blackjetrock/experimental-computer-for-schools/Documentation/1000038513.jpg

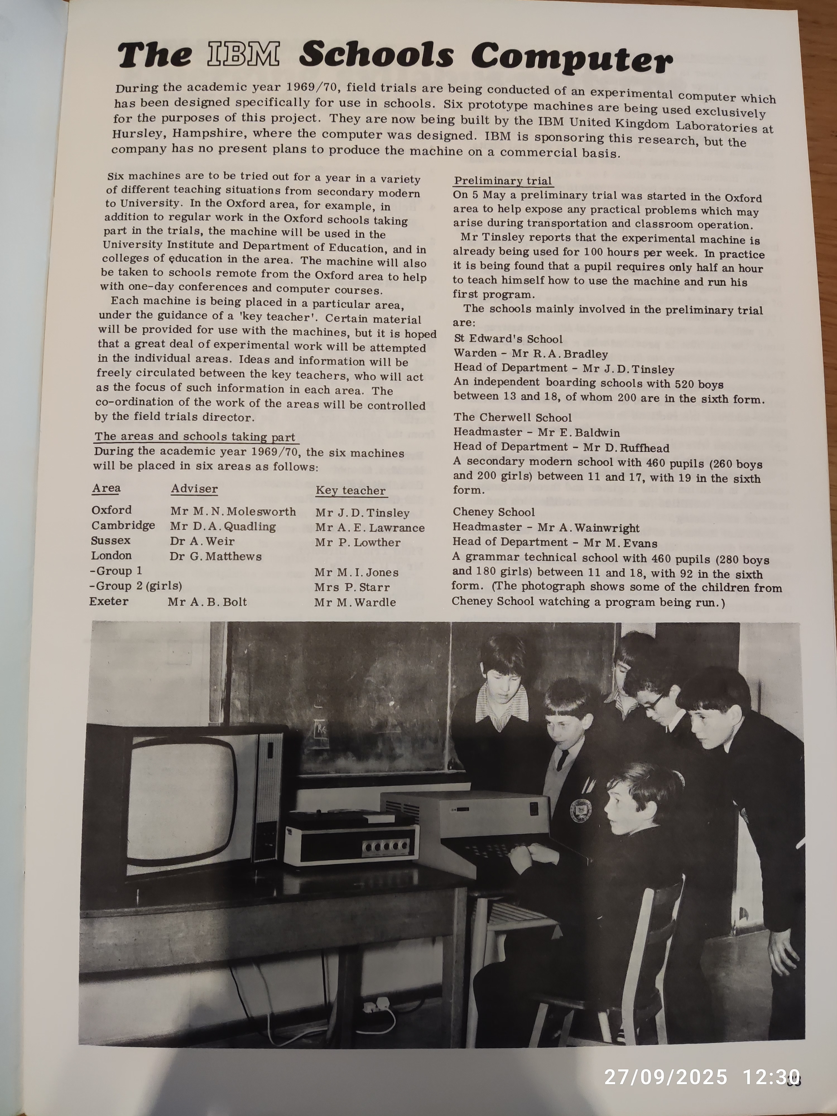
Documentation/1000038513.jpg
