blackjetrock/experimental-computer-for-schools/Documentation/1000038516.jpg

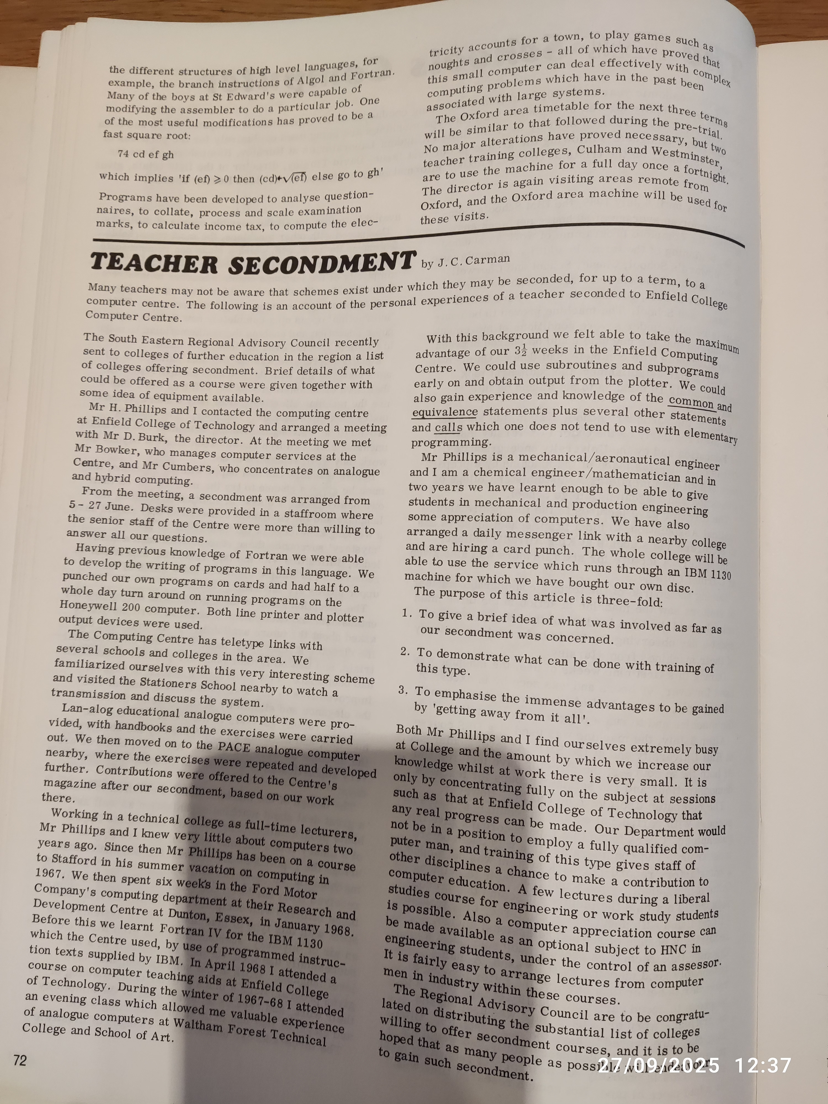
Documentation/1000038516.jpg
