blackjetrock/experimental-computer-for-schools/mechanical/front_panel_62mm_name_recess_only.dxf

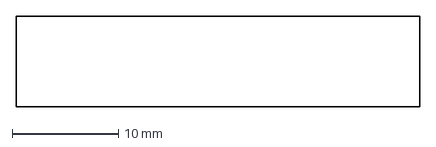
[picture p40: CAD file, 2024-07-29]
mechanical/front_panel_62mm_name_recess_only.dxf
38.0 x 8.50 mm
