blackjetrock/experimental-computer-for-schools/mechanical/3d_models/cased_desktop_left_support.stl

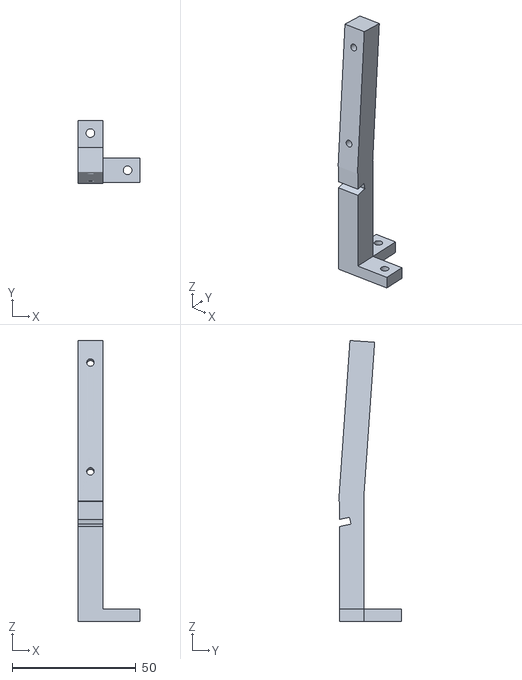
[picture p41: CAD file, 2024-07-29]
mechanical/3d_models/cased_desktop_left_support.stl
25.0 x 25.3 x 113.4
