blackjetrock/experimental-computer-for-schools/mechanical/switch_plate_cutout_1_0mm_tool.dxf

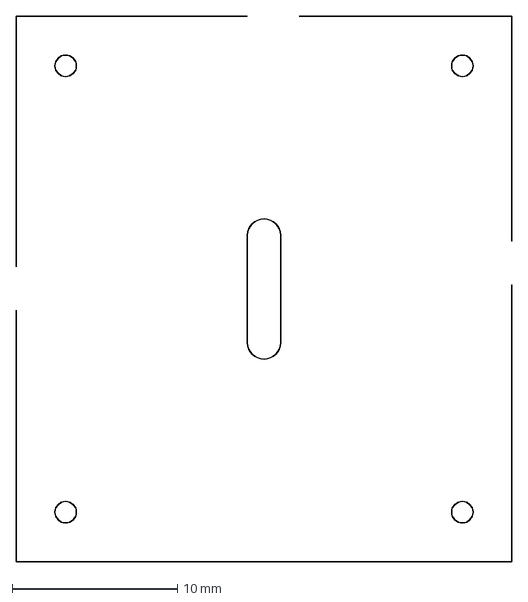
[picture p42: CAD file, 2024-07-29]
mechanical/switch_plate_cutout_1_0mm_tool.dxf
30.0 x 33.0 mm
