blackjetrock/experimental-computer-for-schools/mechanical/3d_models/television_rear_bottom_panel_v2.stl

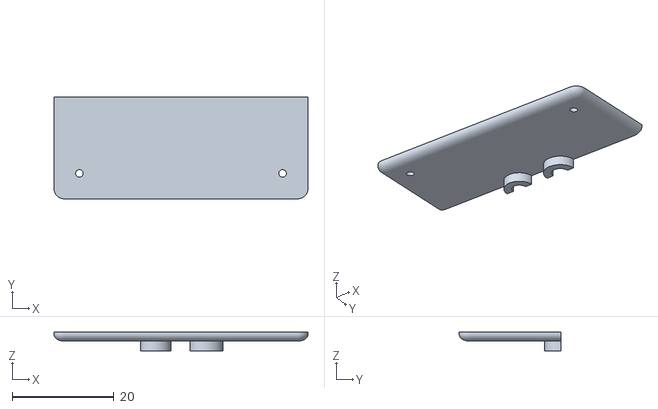
[picture p43: CAD file, 2024-07-29]
mechanical/3d_models/television_rear_bottom_panel_v2.stl
50.0 x 20.0 x 3.65
