blackjetrock/experimental-computer-for-schools/mechanical/switch_plate_cutout_1_5mm_tool.dxf

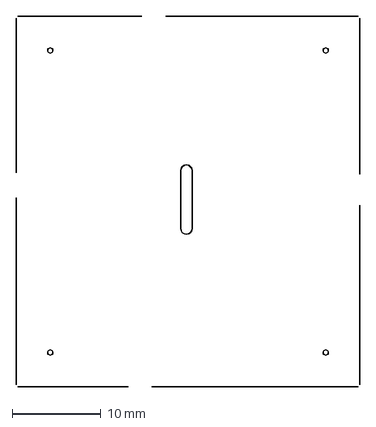
[picture p44: CAD file, 2024-07-23]
mechanical/switch_plate_cutout_1_5mm_tool.dxf
38.7 x 41.7 mm
