blackjetrock/experimental-computer-for-schools/mechanical/3d_models/desktop_pcb_standoff.stl

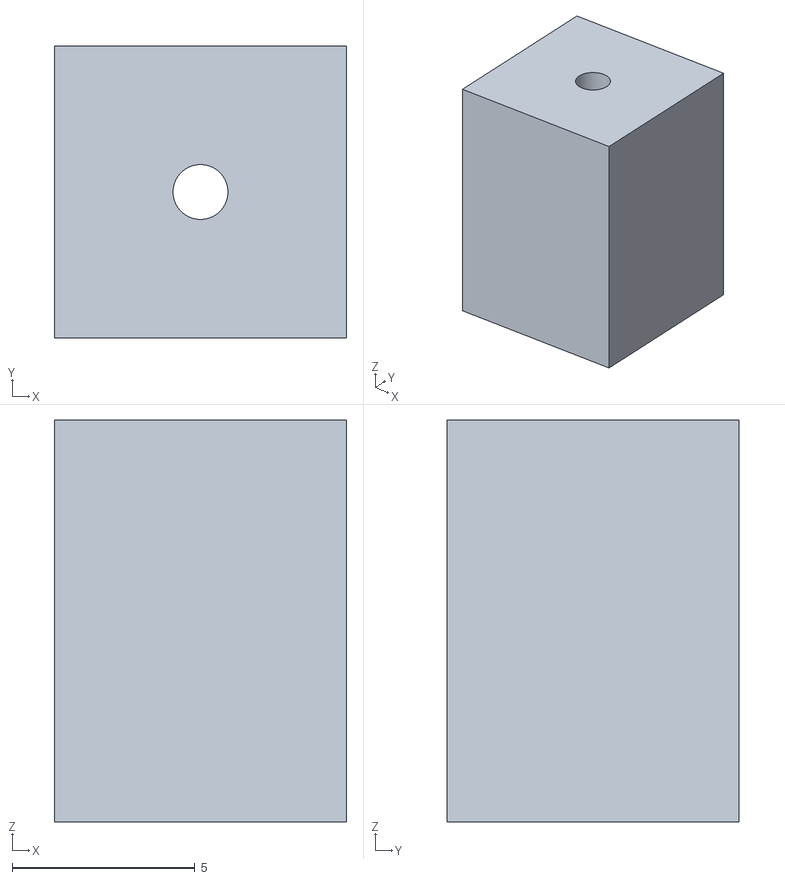
[picture p45: CAD file, 2024-07-29]
mechanical/3d_models/desktop_pcb_standoff.stl
8.00 x 8.00 x 11.0
