blackjetrock/experimental-computer-for-schools/mechanical/switch_plate_cutout.dxf

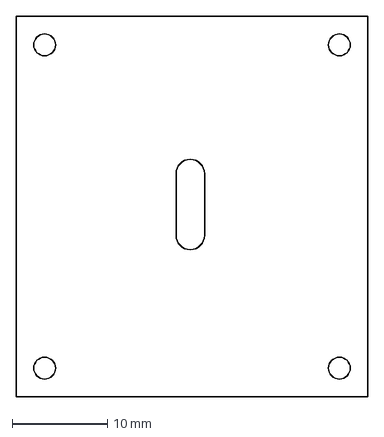
[picture p46: CAD file, 2024-07-23]
mechanical/switch_plate_cutout.dxf
37.0 x 40.0 mm
