blackjetrock/experimental-computer-for-schools/mechanical/3d_models/television_bezel_v2.stl

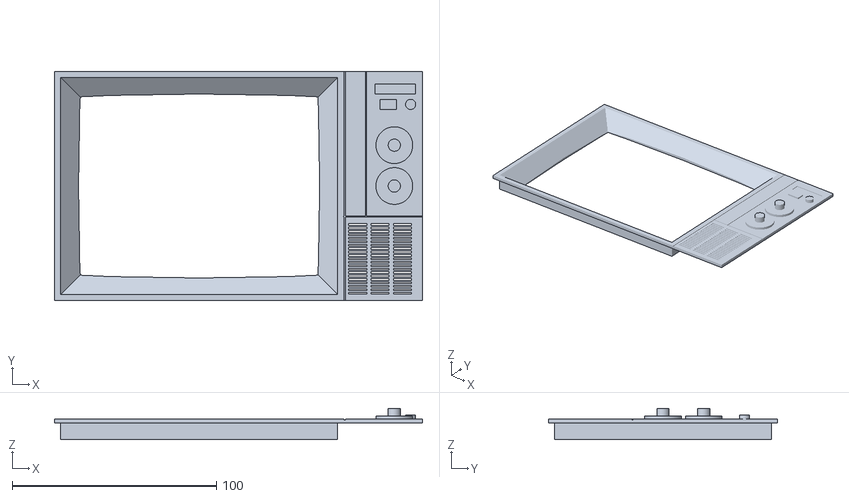
[picture p47: CAD file, 2024-07-29]
mechanical/3d_models/television_bezel_v2.stl
180.3 x 112.4 x 15.3
