blackjetrock/experimental-computer-for-schools/mechanical/front_panel_0mm_tool.dxf

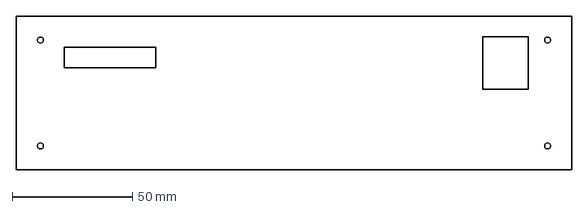
[picture p48: CAD file, 2024-07-23]
mechanical/front_panel_0mm_tool.dxf
231.0 x 64.0 mm
