blackjetrock/experimental-computer-for-schools/mechanical/3d_models/tv_spacer_corner.stl

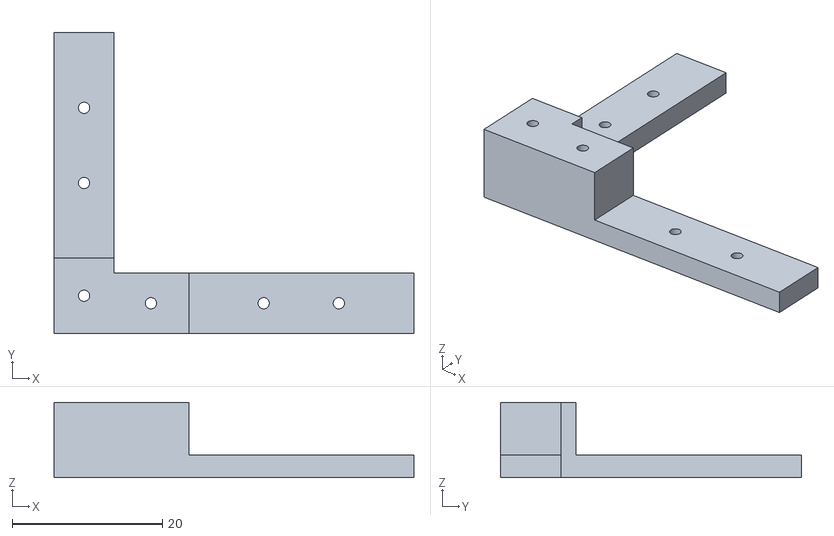
[picture p49: CAD file, 2024-07-29]
mechanical/3d_models/tv_spacer_corner.stl
47.9 x 40.0 x 10.0
