blackjetrock/experimental-computer-for-schools/mechanical/name_plate_vinyl_base_file.dxf

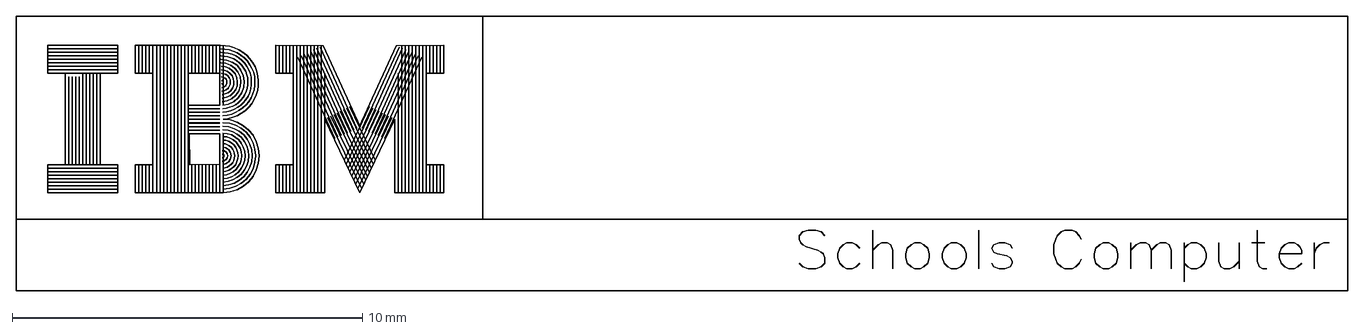
[picture p50: CAD file, 2024-07-23]
mechanical/name_plate_vinyl_base_file.dxf
38.0 x 7.83 mm
