blackjetrock/experimental-computer-for-schools/mechanical/name_plate_writing_borders.dxf

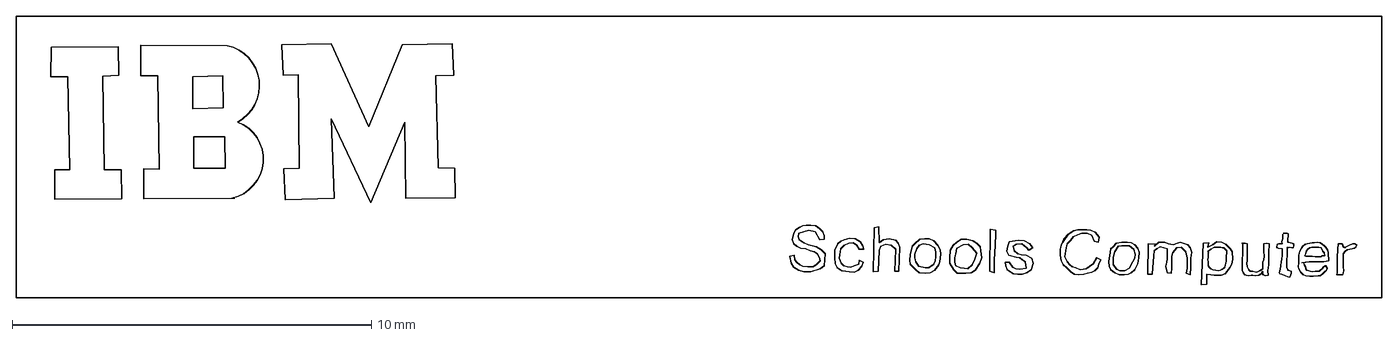
[picture p51: CAD file, 2024-07-23]
mechanical/name_plate_writing_borders.dxf
38.0 x 7.83 mm
