blackjetrock/experimental-computer-for-schools/mechanical/3d_models/overlay_and_front_panel_alignment.dxf

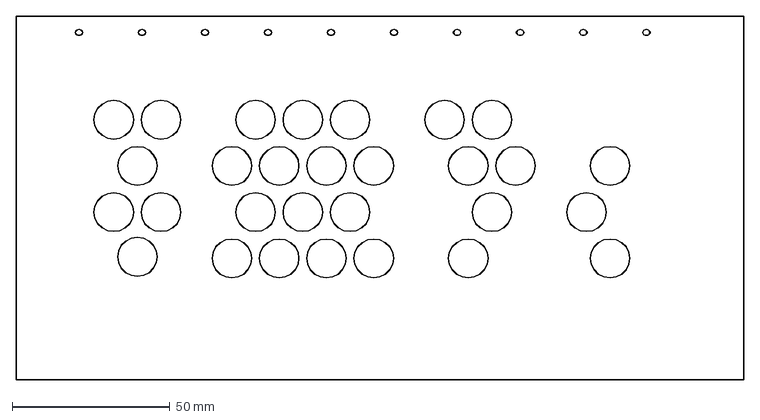
[picture p52: CAD file, 2024-07-01]
mechanical/3d_models/overlay_and_front_panel_alignment.dxf
231.0 x 115.4 mm
