blackjetrock/experimental-computer-for-schools/mechanical/name_plate_writing_borders_lines_tidy_filled_text_only.dxf

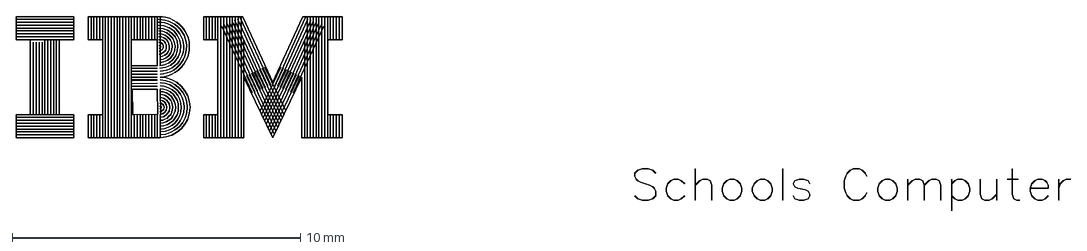
[picture p53: CAD file, 2024-07-23]
mechanical/name_plate_writing_borders_lines_tidy_filled_text_only.dxf
36.6 x 6.75 mm
