blackjetrock/experimental-computer-for-schools/mechanical/3d_models/cased_desktop.dxf

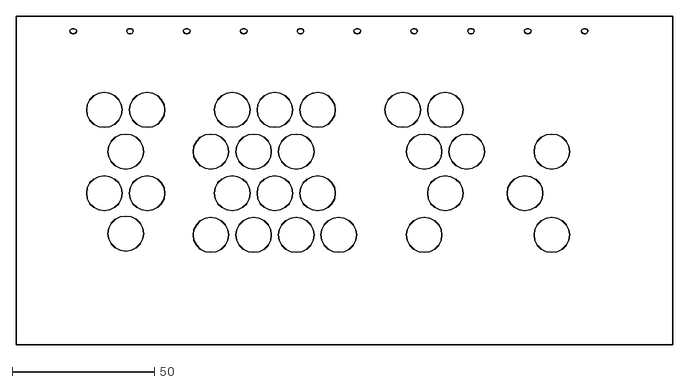
[picture p54: CAD file, 2024-07-01]
mechanical/3d_models/cased_desktop.dxf
231.0 x 115.4
