blackjetrock/experimental-computer-for-schools/mechanical/name_plate_writing_borders_lines_tidy_filled.dxf

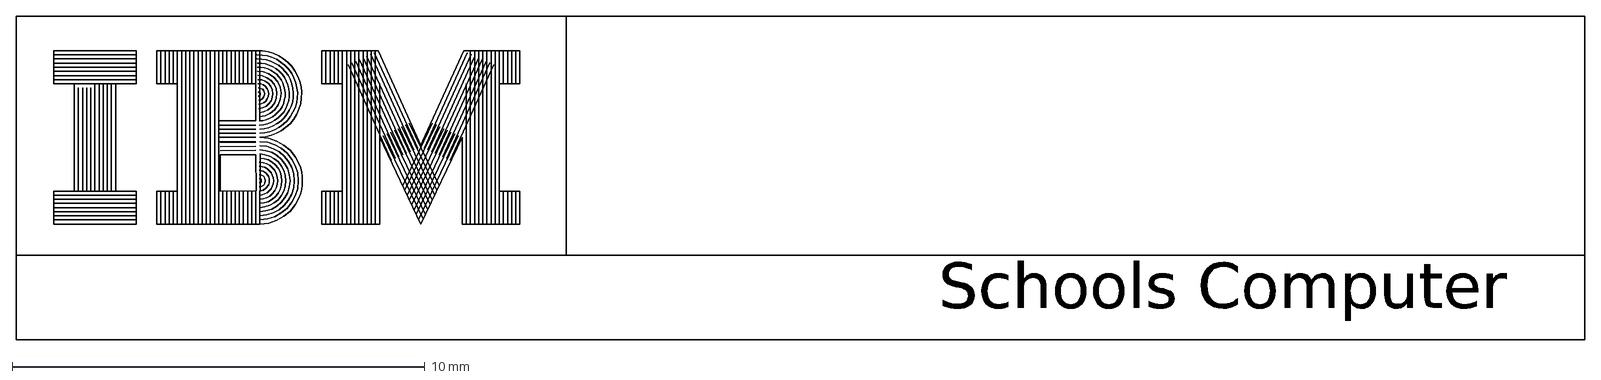
[picture p55: CAD file, 2024-07-23]
mechanical/name_plate_writing_borders_lines_tidy_filled.dxf
Schools Computer
