blackjetrock/experimental-computer-for-schools/mechanical/name_plate_writing_borders_lines_tidy.dxf

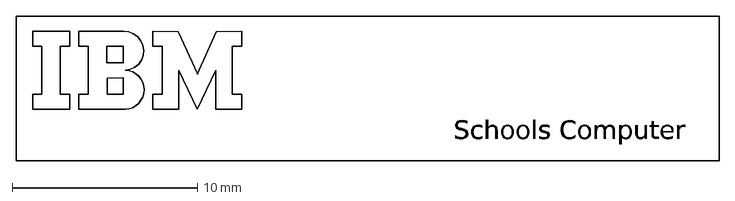
[picture p56: CAD file, 2024-07-23]
mechanical/name_plate_writing_borders_lines_tidy.dxf
Schools Computer
