blackjetrock/experimental-computer-for-schools/mechanical/switch_plate_cutout_1_3mm_tool.dxf

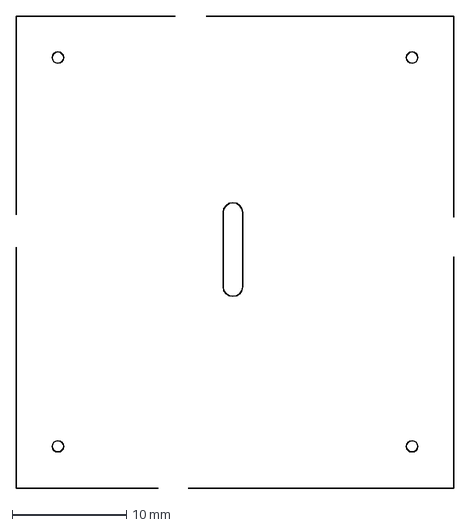
[picture p57: CAD file, 2024-07-23]
mechanical/switch_plate_cutout_1_3mm_tool.dxf
38.3 x 41.3 mm
