blackjetrock/experimental-computer-for-schools/mechanical/front_panel_3mm_tool.dxf

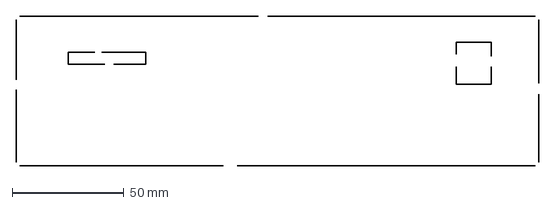
[picture p58: CAD file, 2024-07-23]
mechanical/front_panel_3mm_tool.dxf
234.2 x 67.2 mm
