blackjetrock/experimental-computer-for-schools/mechanical/name_plate.dxf

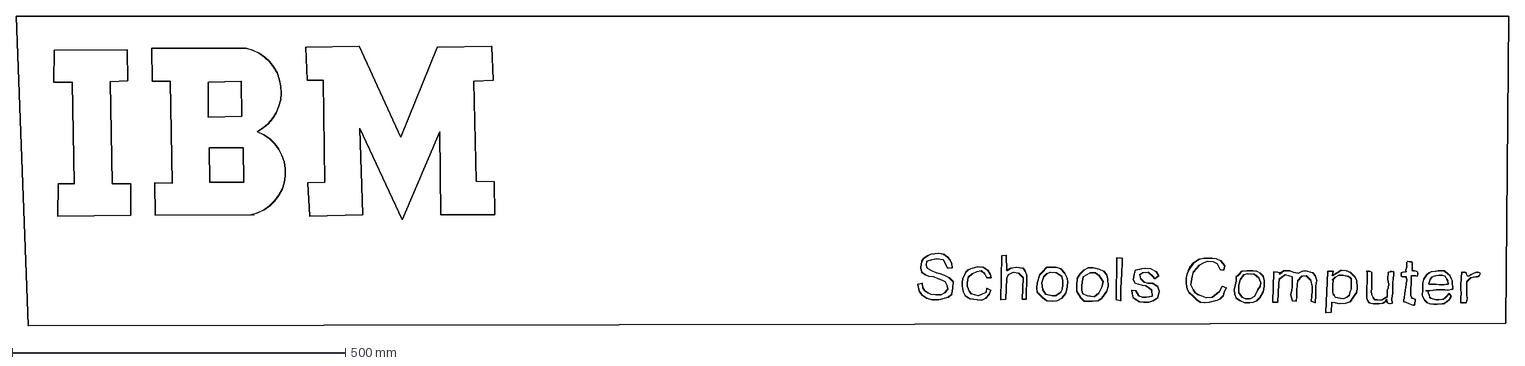
[picture p59: CAD file, 2024-07-23]
mechanical/name_plate.dxf
2239.5 x 463.9 mm
