blackjetrock/experimental-computer-for-schools/mechanical/name_plate_writing_borders_lines_tidy_filled_colour_limits_only.dxf

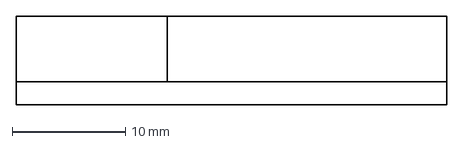
[picture p60: CAD file, 2024-07-23]
mechanical/name_plate_writing_borders_lines_tidy_filled_colour_limits_only.dxf
38.0 x 7.83 mm
