blackjetrock/experimental-computer-for-schools/mechanical/name_plate_writing.dxf

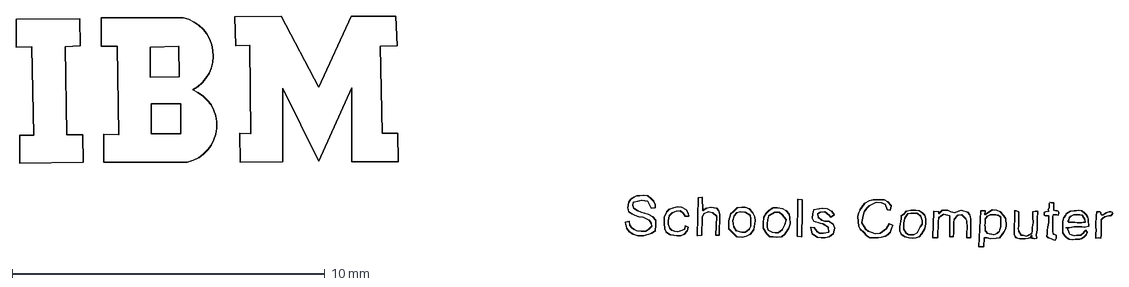
[picture p61: CAD file, 2024-07-23]
mechanical/name_plate_writing.dxf
35.0 x 7.37 mm
