blackjetrock/experimental-computer-for-schools/mechanical/switch_plate_cutout_1mm_tool.dxf

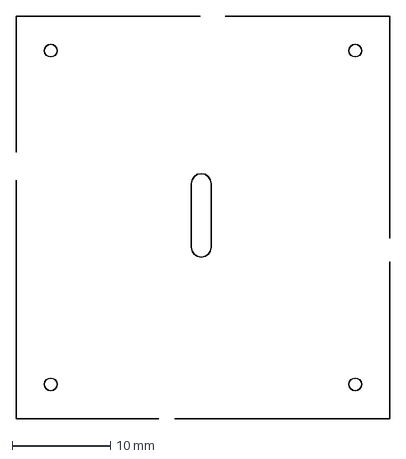
[picture p62: CAD file, 2024-07-23]
mechanical/switch_plate_cutout_1mm_tool.dxf
38.0 x 41.0 mm
