blackjetrock/experimental-computer-for-schools/mechanical/switch_plate_text.dxf

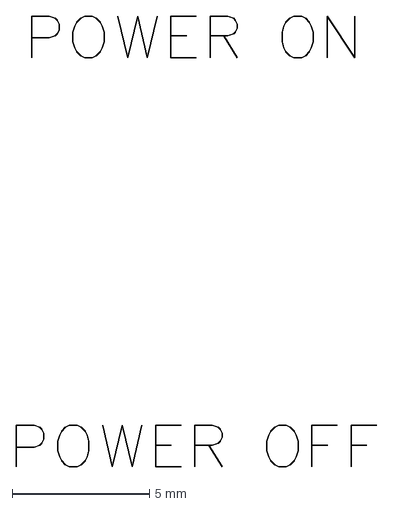
[picture p63: CAD file, 2024-07-23]
mechanical/switch_plate_text.dxf
13.1 x 16.4 mm
