blackjetrock/experimental-computer-for-schools/mechanical/switch_plate.dxf

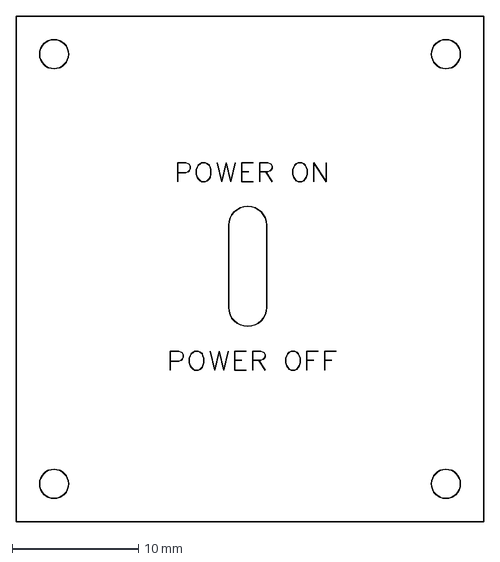
[picture p64: CAD file, 2024-07-23]
mechanical/switch_plate.dxf
37.0 x 40.0 mm
