blackjetrock/experimental-computer-for-schools/mechanical/Untitled.dxf

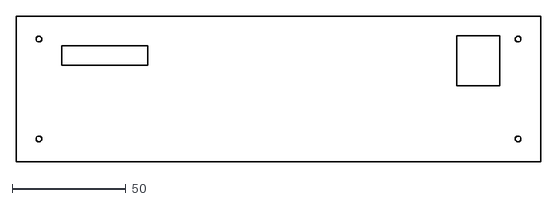
[picture p65: CAD file, 2024-07-16]
mechanical/Untitled.dxf
231.0 x 64.0
