blackjetrock/experimental-computer-for-schools/mechanical/front_panel2.dxf

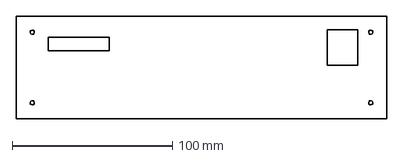
[picture p66: CAD file, 2024-07-16]
mechanical/front_panel2.dxf
231.0 x 64.0 mm
