blackjetrock/experimental-computer-for-schools/mechanical/test.dxf

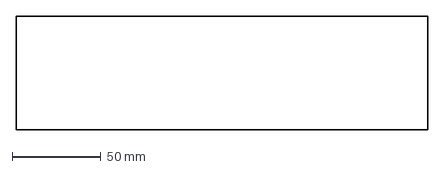
[picture p67: CAD file, 2024-07-16]
mechanical/test.dxf
231.0 x 64.0 mm
