blackjetrock/experimental-computer-for-schools/mechanical/front_panel_cnc_tool_1_3mm.dxf

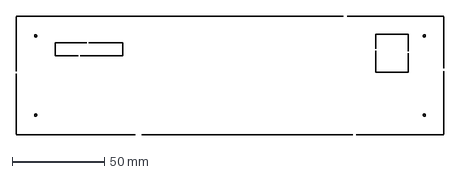
[picture p68: CAD file, 2024-07-16]
mechanical/front_panel_cnc_tool_1_3mm.dxf
232.3 x 64.3 mm
