blackjetrock/experimental-computer-for-schools/mechanical/front_panel.dxf

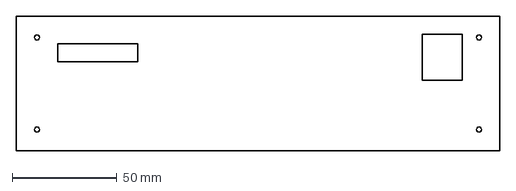
[picture p69: CAD file, 2024-07-16]
mechanical/front_panel.dxf
231.0 x 64.0 mm
