blackjetrock/experimental-computer-for-schools/mechanical/front_panel_cnc_tool_1_0mm.dxf

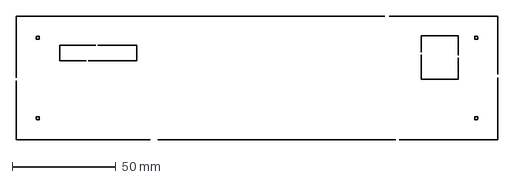
[picture p70: CAD file, 2024-07-14]
mechanical/front_panel_cnc_tool_1_0mm.dxf
232.0 x 59.6 mm
