blackjetrock/experimental-computer-for-schools/mechanical/esc_desktop_case_grill_cnc.dxf

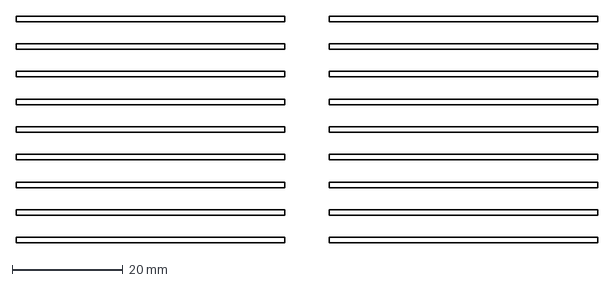
[picture p71: CAD file, 2024-07-14]
mechanical/esc_desktop_case_grill_cnc.dxf
105.0 x 41.0 mm
