blackjetrock/experimental-computer-for-schools/mechanical/name_panel.dxf

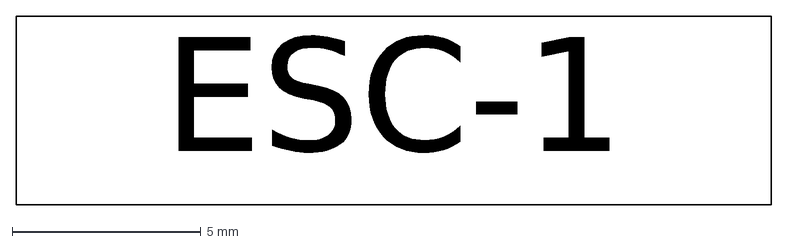
[picture p73: CAD file, 2024-07-13]
mechanical/name_panel.dxf
ESC-1
