blackjetrock/experimental-computer-for-schools/mechanical/knob_label_1.dxf

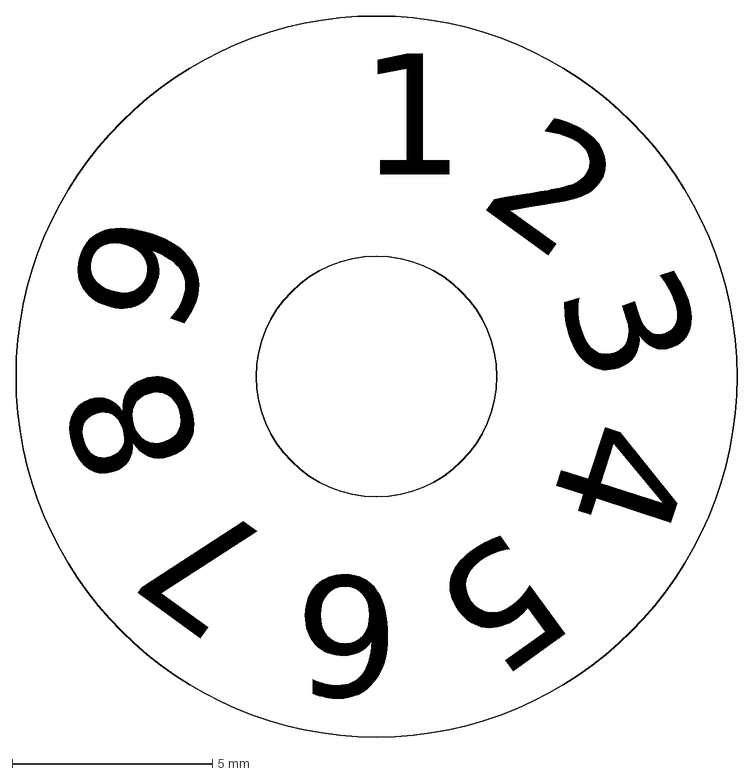
[picture p74: CAD file, 2024-07-13]
mechanical/knob_label_1.dxf
1
3
2
4
5
6
7
8
9
