blackjetrock/experimental-computer-for-schools/mechanical/knob_label_2.dxf

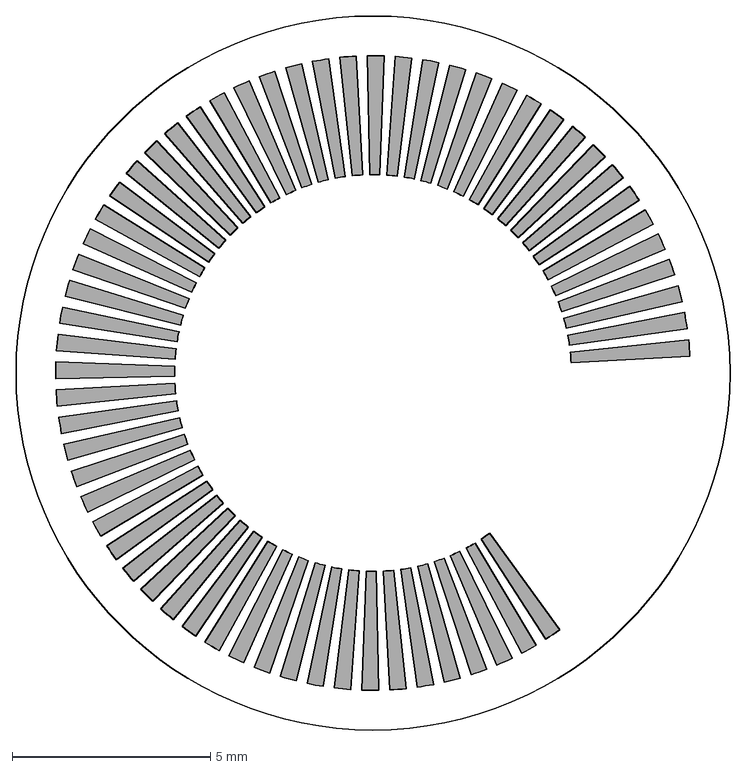
[picture p75: CAD file, 2024-07-13]
mechanical/knob_label_2.dxf
18.0 x 18.0 mm
