blackjetrock/experimental-computer-for-schools/mechanical/kb_holes.dxf

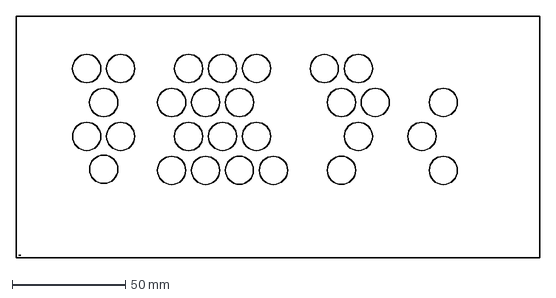
[picture p76: CAD file, 2024-06-30]
mechanical/kb_holes.dxf
231.0 x 106.5 mm
