blackjetrock/experimental-computer-for-schools/mechanical/kb_holes_bevelled.dxf

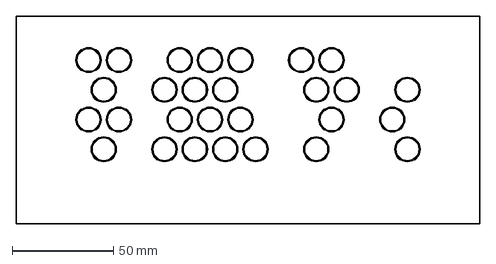
[picture p77: CAD file, 2024-06-29]
mechanical/kb_holes_bevelled.dxf
229.0 x 102.3 mm
