blackjetrock/experimental-computer-for-schools/firmware/pico_main/experimental_schools_computer.c

//////////////////////////////////////////////////////////////////////////////
//
// Experimental Schools Computer Simulator
//
////////////////////////////////////////////////////////////////////////////////
//
// Simulates the IBM experimental schools computer
//
// Runs on RP Pico
// 0.96" OLED display
// Tactile switch keys
//
// USB CLI
// Wifi hot spot with screen display 
//
////////////////////////////////////////////////////////////////////////////////

#include "switches.h"
#include "version.h"

#pragma GCC diagnostic ignored "-Wwrite-strings"

#include <ctype.h>
#include <math.h>
#include <stdarg.h>
#include <stdio.h>
#include <stdlib.h>
#include <string.h>
#include <stdint.h>

#include "pico/stdlib.h"
#include "hardware/pio.h"
#include "hardware/dma.h"
#include "hardware/irq.h"
#include "hardware/flash.h"
#include "hardware/clocks.h"
#include "hardware/structs/bus_ctrl.h"

#define DEBUG_STOP_LOOP while(1) {}

// Some logic to analyse:

#include "hardware/structs/pwm.h"
#include "pico/multicore.h"
#include "pico/bootrom.h"

#include "oled.h"
#include "sdcard.h"

#include "fsms.h"
#include "esc_fsms.h"

#include "esc.h"
#include "esc_desktop_display.h"
#include "extracode.h"

////////////////////////////////////////////////////////////////////////////////

int status[7];
int kbd_scan_code = 0;

#define CHAR_MS_DELAY 20

//------------------------------------------------------------------------------
//
// Decode key tokens
//

KEY_INFO key_info[] =
  {
    {"KI RESET   ", TOK_KEY_KI_RESET},
    {"A          ", TOK_KEY_A},
    {"B          ", TOK_KEY_B},
    {"C          ", TOK_KEY_C},
    {"0          ", TOK_KEY_0},
    {"1          ", TOK_KEY_1},
    {"2          ", TOK_KEY_2},
    {"3          ", TOK_KEY_3},
    {"4          ", TOK_KEY_4},
    {"5          ", TOK_KEY_5},
    {"6          ", TOK_KEY_6},
    {"7          ", TOK_KEY_7},
    {"8          ", TOK_KEY_8},
    {"9          ", TOK_KEY_9},
    {"RUN        ", TOK_KEY_RUN},
    {"STOP       ", TOK_KEY_STOP},
    {"RELOAD     ", TOK_KEY_RELOAD},
    {"CHECK      ", TOK_KEY_CHECK},
    {"DUMP       ", TOK_KEY_DUMP},
    {"LOAD IAR   ", TOK_KEY_LOAD_IAR},
    {"LOAD ADDR  ", TOK_KEY_LOAD_ADDR},
    {"LOAD STORE ", TOK_KEY_LOAD_STORE},
    {"DECR ADDR  ", TOK_KEY_DECR_ADDR},
    {"INCR ADDR  ", TOK_KEY_INCR_ADDR},
    {"NORM RESET ", TOK_KEY_NORMAL_RESET},
    {"CLEAR      ", TOK_KEY_CLEAR},
    {"DOT        ", TOK_KEY_DOT},
    {"MINUS      ", TOK_KEY_MINUS},
  };

#define NUM_KEY_INFO (sizeof(key_info)/sizeof(KEY_INFO))

char *key_name(int tok)
{
  for(int i=0; i<NUM_KEY_INFO; i++)
    {
      if( key_info[i].tok == tok )
        {
          return(key_info[i].name);
        }
    }
  return("????");
}

////////////////////////////////////////////////////////////////////////////////
//
// Tests
//

#define MAX_TEST_FAIL_BUFFER 160

// Initialise registers and store
typedef enum _INIT_CODE
  {
    IC_SET_REG_N = 10,
    IC_SET_REG_V,
    IC_SET_STORE_A,
    IC_SET_STORE_V,
    IC_END,
  } INIT_CODE;

typedef struct _INIT_INFO
{
  INIT_CODE code;
  uint64_t   n;
} INIT_INFO;

// The following enum is also used to identify registers other than R0..9
// when testing results. E.g. IAR

typedef enum _TEST_CODE
  {
    TC_REG_N = 20,
    TC_REG_IAR,
    TC_REG_LINK,
    TC_REG_ADDR,
    TC_CL,
    TC_REG_KI,
    TC_STORE_N,
    TC_MUST_BE,
    TC_MUST_BE_STOPPED,
    TC_MUST_BE_NOT_STOPPED,
    TC_END_SECTION,    // End of sub section results. Check up to here (or a TC_END) by TOK_TEST_CHECK_RES token
    // Do not put a spurious TC_SECTION_END before a TC_END
    TC_END,
  } TEST_CODE;

char *tc_names[] =
  {
    "TC_REG_N",
    "TC_REG_IAR",
    "TC_REG_LINK",
    "TC_REG_ADDR",
    "TC_CL",
    "TC_REG_KI",
    "TC_STORE_N",
    "TC_MUST_BE",
    "TC_MUST_BE_STOPPED",
    "TC_MUST_BE_NOT_STOPPED",
    "TC_END_SECTION",
    "TC_END",
  };

#define MAX_TC_REG_BUF 20

#define TEST_LOAD_STORE_LEN 100

typedef struct _TEST_LOAD_STORE
{
  int data[TEST_LOAD_STORE_LEN];
} TEST_LOAD_STORE;

typedef struct _TEST_INFO
{
  TEST_CODE       code;
  uint64_t        n;
} TEST_INFO;

typedef struct _ESC_TEST_INFO
{
  char            *desc;
  INIT_INFO       *init_codes;
  TOKEN           *seq;
  TEST_INFO       *result_codes;
  int              passed;
  TEST_LOAD_STORE *store_data;
  char             fail_text[MAX_TEST_FAIL_BUFFER];
} ESC_TEST_INFO;

#define NUM_TESTS (sizeof(tests)/sizeof(ESC_TEST_INFO))

////////////////////////////////////////////////////////////////////////////////

#define TEXT_PARAMETER_LEN 40

////////////////////////////////////////////////////////////////////////////////
//
//
#define MAX_ERROR_BUFFER 200

void error_msg(char *fmt, ...)
{
  char line[MAX_ERROR_BUFFER+1];
  
  va_list args;
  va_start(args, fmt);

  vsnprintf(line, MAX_ERROR_BUFFER, fmt, args);
  va_end(args);

#if ERRORS_ON
  printf("\n*** %s ***\n", line);
#endif
  
}

void warning_msg(char *fmt, ...)
{
  char line[MAX_ERROR_BUFFER+1];
  
  va_list args;
  va_start(args, fmt);

  vsnprintf(line, MAX_ERROR_BUFFER, fmt, args);
  va_end(args);

  printf("\n*** WARNING: %s ***\n", line);
}



char tc_reg_buffer[MAX_TC_REG_BUF+1];

////////////////////////////////////////////////////////////////////////////////

void serial_help(void);
void prompt(void);
void prompt_breakpoint(void);

int write_state_to_file(ESC_STATE *es, char *fn);
int read_file_into_state(char *fn, ESC_STATE *es);
int cat_file(char *fn);

int wfn_iar_address(ESC_STATE *es, void *fi, char *line);
int wfn_iar_a_flag(ESC_STATE *es, void *fi, char *line);
int wfn_breakpoint_address(ESC_STATE *es, void *fi, char *line);
int wfn_breakpoint_a_flag(ESC_STATE *es, void *fi, char *line);
int wfn_kb_register(ESC_STATE *es, void *fi, char *line);
#if 0
int wfn_address_register(ESC_STATE *es, void *fi, char *line);
#endif
int wfn_link_register(ESC_STATE *es, void *fi, char *line);
int wfn_instruction_register(ESC_STATE *es, void *fi, char *line);
int wfn_store_data(ESC_STATE *es, void *fi, char *line);
int wfn_store(ESC_STATE *es, void *fi, char *line);
int wfn_suppressed_display(ESC_STATE *es, void *fi, char *line);
int wfn_step_extracode(ESC_STATE *es, void *fi, char *line);

void update_computer_display(ESC_STATE *es);
void register_assign_register_uint64(ESC_STATE *s, int dest, uint64_t n);
REGISTER_DOUBLE_WORD read_any_size_register(ESC_STATE *s, int n);
REGISTER_DOUBLE_WORD read_any_size_register_absolute(ESC_STATE *s, int n);

ESC_TEST_INFO tests[];
void display_on_line(ESC_STATE *s, int display, int line_no, char *fmt, ...);
char *display_register_and_contents(ESC_STATE *s, int regno);
char *display_store_and_contents(ESC_STATE *s, SINGLE_WORD address);
char *display_store_word(SINGLE_WORD w);
int display_two_any_size_register_on_line(ESC_STATE *s, int display, int lineno, int regno1, int regno2, int contents);

void stage_a_display(ESC_STATE *s, int display, int a);
void stage_b_display(ESC_STATE *s, int display, int a);
void stage_c_display(ESC_STATE *s, int display, int a);

#define NO_CONTENTS 0
#define CONTENTS    1

//------------------------------------------------------------------------------

int display_any_size_register_on_line(ESC_STATE *s, int display, int line_no, int regno, int contents);

void clear_lines_3_to_6(ESC_STATE *s, int display);
void clear_line(ESC_STATE *s, int display, int n);
void clear_display(ESC_STATE *s, int display);

//------------------------------------------------------------------------------

volatile uint32_t touch_key_raw = 0;
int get_qt_key_code(void);
////////////////////////////////////////////////////////////////////////////////
//
// Register access
//

// Register identiiers.
// 0..9 are R0..R9

typedef enum _REGN
  {
    REGN_0 = 0,
    REGN_1 = 1,
    REGN_2 = 2,
    REGN_3 = 3,
    REGN_4 = 4,
    REGN_5 = 5,
    REGN_6 = 6,
    REGN_7 = 7,
    REGN_8 = 8,
    REGN_9 = 9,
    REGN_IAR,
    REGN_AUX_IAR,
  } REGN;

void write_register(ESC_STATE *s, REGN n, REGISTER_DOUBLE_WORD data)
{
  switch(n)
    {
    case REGN_0:
    case REGN_1:
    case REGN_2:
    case REGN_3:
    case REGN_4:
    case REGN_5:
    case REGN_6:
    case REGN_7:
      s->store[200+n] = (REGISTER_SINGLE_WORD)data;
      break;

    case REGN_8:
    case REGN_9:
      // R8 and R9 are in two locations each. Lower address is lower half of register
      s->store[200+n] = (REGISTER_SINGLE_WORD) (data & 0xFFFFFFFF);
      s->store[210+n] = (REGISTER_SINGLE_WORD) ((data & 0xFFFFFFFF00000000) >> 32);
      break; 
    }
}

// Read any register
// For SW, cast result.

REGISTER_DOUBLE_WORD read_register(ESC_STATE *s, REGN n)
{
  switch(n)
    {
    case REGN_0:
    case REGN_1:
    case REGN_2:
    case REGN_3:
    case REGN_4:
    case REGN_5:
    case REGN_6:
    case REGN_7:
      return (REGISTER_DOUBLE_WORD)(s->store[200+n]);
      break;

    case REGN_8:
    case REGN_9:
      // R8 and R9 are in two locations each. Lower address is lower half of register
      return ( ((REGISTER_DOUBLE_WORD)(s->store[200+n])) | (((REGISTER_DOUBLE_WORD)(s->store[210+n])) << 32));
      break; 
    }
}

////////////////////////////////////////////////////////////////////////////////

char *tc_reg_name(TEST_CODE tc)
{
  if( tc < TC_REG_N )
    {
      snprintf(tc_reg_buffer, MAX_TC_REG_BUF, "%d", tc);
      return(tc_reg_buffer);
    }
  
  return(tc_names[tc-TC_REG_N]);
}

// Load the store before running the test. Words are terminated by a -1


//------------------------------------------------------------------------------
//
// Test failure information
//

char test_fail_buffer[MAX_TEST_FAIL_BUFFER];

void clear_test_fail_buffer(void)
{
  test_fail_buffer[0] = '\0';
}


// Add more information to the test fail buffer
void test_fail_info(char *fmt, ...)
{
  char line[MAX_TEST_FAIL_BUFFER+1];
  
  va_list args;
  va_start(args, fmt);

  vsnprintf(line, MAX_TEST_FAIL_BUFFER, fmt, args);
  va_end(args);

  printf("\n-----------%s---", line);
  
  // How much space is available for more text?
  // Include a space delimiter and the newline at the end.
  int n = MAX_TEST_FAIL_BUFFER-strlen(test_fail_buffer)-1-1;

  printf("\nn=%d, strlen(tfb)=%d strlen(line)=%d", n, strlen(test_fail_buffer), strlen(line));
  
  if( n < 0 )
    {
      test_fail_buffer[0] = '!';
      printf("\n***%s***%d**", test_fail_buffer, n);
      return;
    }

  strcat(test_fail_buffer, " ");
  strncat(test_fail_buffer, line, n);

  printf("\n+++++++++++%s+++", test_fail_buffer);
}

////////////////////////////////////////////////////////////////////////////////
//

void load_store_from_test(ESC_STATE *s, int test_number)
{
  // Load the store
  
  for(int i=0; (i<TEST_LOAD_STORE_LEN) && (tests[test_number].store_data->data[i] != -1); i++)
    {
      s->store[i] = tests[test_number].store_data->data[i];
    }
}

////////////////////////////////////////////////////////////////////////////////

int keypress = 0;
int parameter = 0;
int parameter_a_flag = 0;

int auto_increment_parameter = 0;
int auto_increment_address   = 0;
char text_parameter[TEXT_PARAMETER_LEN+1] = "";
int address               = 0;
int test_number           = 0;
int test_run_single_test  = 0;
int test_running          = 0;
int test_waiting_for_stop = 0;
int test_done_init        = 0;
int test_step             = 0;

////////////////////////////////////////////////////////////////////////////////
//
// GPIOs
//

void set_gpio_output(const int gpio)
{
  gpio_init(gpio);
  gpio_set_dir(gpio, GPIO_OUT);
}

void set_gpio_input(const int gpio)
{
  gpio_init(gpio);
  gpio_set_dir(gpio, GPIO_IN);
}

#if ESC_TYPE_DESKTOP

// We set GPIOs and the UART

const int PIN_QT_DRDY =  26;
const int PIN_QT_WS   =  17;

void set_kbd_gpios(void)
{
  set_gpio_input(PIN_QT_DRDY);

  // Set WAKE/SYNC high
  set_gpio_output(PIN_QT_WS);
  gpio_put(PIN_QT_WS, 1);

  // Set the GPIO pin mux to the UART - 12 is TX, 13 is RX
  // Takes over GPIO directions
  gpio_set_function(12, GPIO_FUNC_UART);
  gpio_set_function(13, GPIO_FUNC_UART);

  printf("\nQT Baud rate set to %d", uart_init (uart0, 9600));
  uart_set_format (uart0, 8, 1, UART_PARITY_NONE);

}


#endif

#if ESC_TYPE_SMALL

// KBD
const int PIN_KBD_DRV0 =  0;
const int PIN_KBD_DRV1 =  1;
const int PIN_KBD_DRV2 =  2;
const int PIN_KBD_DRV3 =  3;

const int PIN_KBD_SENS0 =   4;
const int PIN_KBD_SENS1 =   5;
const int PIN_KBD_SENS2 =   6;
const int PIN_KBD_SENS3 =   7;
const int PIN_KBD_SENS4 =   8;
const int PIN_KBD_SENS5 =   9;
const int PIN_KBD_SENS6 =  10;



//------------------------------------------------------------------------------
//
// Set up GPIOs for the keyboard

void kbd_gpio_drv(const int gpio)
{
  gpio_init(gpio);
  gpio_set_dir(gpio, GPIO_OUT);
}

void kbd_gpio_sens(const int gpio)
{
  gpio_init(gpio);
  gpio_set_dir(gpio, GPIO_IN);
  gpio_set_pulls(gpio, 0, 1);
}

const int kbd_drv_gpios[] =
  {
    PIN_KBD_DRV0,   
    PIN_KBD_DRV1,   
    PIN_KBD_DRV2,   
    PIN_KBD_DRV3,   
  };

#define NUM_KBD_DRV (sizeof(kbd_drv_gpios)/sizeof(const int))

const int kbd_sens_gpios[] =
  {
    PIN_KBD_SENS0,   
    PIN_KBD_SENS1,   
    PIN_KBD_SENS2,   
    PIN_KBD_SENS3,   
    PIN_KBD_SENS4,   
    PIN_KBD_SENS5,   
    PIN_KBD_SENS6,
  };

#define NUM_KBD_SENS (sizeof(kbd_sens_gpios)/sizeof(const int))

void set_kbd_gpios(void)
{
  kbd_gpio_drv(PIN_KBD_DRV0);
  kbd_gpio_drv(PIN_KBD_DRV1);
  kbd_gpio_drv(PIN_KBD_DRV2);
  kbd_gpio_drv(PIN_KBD_DRV3);

  kbd_gpio_sens(PIN_KBD_SENS0);
  kbd_gpio_sens(PIN_KBD_SENS1);
  kbd_gpio_sens(PIN_KBD_SENS2);
  kbd_gpio_sens(PIN_KBD_SENS3);
  kbd_gpio_sens(PIN_KBD_SENS4);
  kbd_gpio_sens(PIN_KBD_SENS5);
  kbd_gpio_sens(PIN_KBD_SENS6);
    
}

int kbd_read_sense(void)
{
  int res = 0;
  
  for(int i=0; i<NUM_KBD_SENS; i++)
    {
      if( gpio_get(kbd_sens_gpios[i]) )
	{
	  res |= 1<<i;
	}
    }
  return(res);
}

// Scan the keyboard.
// Drive each drive line and scan the sense lines, then feed the keycodes seen
// into a simple state machine for debounce.
// Debounce counts up to  press and dow to a release
// Key codes injected into FSM on press

#define NUM_KBD_T_SLOTS  10

enum
  {
    KBD_DB_STATE_IDLE = 1,
    KBD_DB_STATE_PRESSING,
    KBD_DB_STATE_RELEASING,
  };

int kbd_t_slot = 0;
int kbd_drv_i = 0;
int kbd_sense = 0;
int kbd_output_scan_code = 0;
int kbd_last_output_scan_code = 0;

int kbd_last_scan_code = 0;
int kbd_db_state = KBD_DB_STATE_IDLE;

#define KBD_DB_COUNT_MAX 100
int kbd_db_count = 0;

void cli_kbd_dump(void)
{
  printf("\nKeyboard State\n");

  printf("\nScan code:%03X Last scan code:%03X", kbd_scan_code, kbd_last_scan_code);
  printf("\nOutput san code:%03X", kbd_output_scan_code);

  printf("\nI:%d  T Slot:%d", kbd_drv_i, kbd_t_slot);
  printf("\nSense:%02X", kbd_sense);
}

// Drive required sense line
void kbd_drive(void)
{
  int i;

  // Turn drive lines off
  for(i=0; i<NUM_KBD_DRV; i++)
    {
      gpio_put(kbd_drv_gpios[i], 0);
    }
  
  // Move to next drive line
  kbd_drv_i = (kbd_drv_i + 1 ) % NUM_KBD_DRV;
  
  // Drive required line
  gpio_put(kbd_drv_gpios[kbd_drv_i], 1);
}

// Send a keypress to the FSM

struct _KEYMAP
{
  int scan_code;
  TOKEN token;
}
  key_map[] =
  {
    {0x1C0, TOK_KEY_CLEAR},
    {0x101, TOK_KEY_MINUS},
    {0x102, TOK_KEY_DOT},
    {0x090, TOK_KEY_0},
    {0x104, TOK_KEY_1},
    {0x108, TOK_KEY_2},
    {0x110, TOK_KEY_3},
    {0x120, TOK_KEY_4},
    {0x140, TOK_KEY_5},
    {0x081, TOK_KEY_6},
    {0x082, TOK_KEY_7},
    {0x084, TOK_KEY_8},
    {0x088, TOK_KEY_9},
    {0x010, TOK_KEY_DUMP},
    {0x020, TOK_KEY_CHECK},
    {0x040, TOK_KEY_RELOAD},

    {0x1A0, TOK_KEY_NORMAL_RESET},
    {0x002, TOK_KEY_KI_RESET},
    {0x181, TOK_KEY_LOAD_IAR},
    {0x182, TOK_KEY_LOAD_ADDR},
    {0x190, TOK_KEY_INCR_ADDR},
    {0x188, TOK_KEY_DECR_ADDR},
    {0x184, TOK_KEY_LOAD_STORE},
    {0x0A0, TOK_KEY_A},
    {0x0C0, TOK_KEY_B},
    {0x001, TOK_KEY_C},
    {0x004, TOK_KEY_RUN},
    {0x008, TOK_KEY_STOP},
  };

#define NUM_KEY_MAPS (sizeof(key_map)/sizeof( struct _KEYMAP))
  
void kbd_queue_key(int k)
{
  for(int i=0; i<NUM_KEY_MAPS; i++)
    {
      if( k == key_map[i].scan_code )
	{
	  queue_token(key_map[i].token);
#if DEBUG_KEYS
          printf("\nKey: %s", key_name(key_map[i].token)); 
#endif
	  return;
	}
    }
}

#endif

//------------------------------------------------------------------------------

void cli_version(void)
{
  printf("\nVersion:1.1.%d Compile time:%s %s\n", VERSION_INC, __DATE__, __TIME__);
}

//------------------------------------------------------------------------------

void cli_display_test(void)
{
  escdd_main();
}

int test_loop_count = 0;
#define TEST_EVERY_N_LOOPS  10

int test_res_i = 0;

int last_token = TOK_NONE;

// read scan code
void kbd_read(ESC_STATE *s)
{
#if 0

  // Hopefully transient error during extracode implementation
  if( s->store[168] == 0 )
    {
      printf("\n**** 168 == 0 *******\n\n");
      while(0)
        {
        }
    }
  
#endif
  

#if ESC_TYPE_SMALL  
  // If the drive index is zero then reset the scan code
  if( kbd_drv_i == 0 )
    {
      kbd_scan_code = 0;
    }
  
  kbd_sense = kbd_read_sense();

  // Only build scan code if a key is pressed
  if( kbd_sense != 0 )
    {
      // Save last scan code
      kbd_last_scan_code = kbd_scan_code;
      
      // Build scan code
      kbd_scan_code = (kbd_drv_i << 7) | kbd_sense;
    }
#endif

#if ESC_TYPE_DESKTOP

  
  // Get the keycode of the key currently pressed if there is one.
  kbd_scan_code = get_qt_key_code();

  if( kbd_scan_code == TOK_NONE )
    {
      last_token = TOK_NONE;
    }
  
  if( kbd_scan_code != TOK_NONE )
    {
      // Key pressed, new key?
      if( kbd_scan_code != last_token )
	{
	  queue_token(kbd_scan_code);
	}
      
      last_token = kbd_scan_code;
    }
#endif
  else
    {
      // No key pressed, check for a running test after N idle loops
      // We allow the FSMs to run for a while between keystrokes
      // If we are waiting for a stop condition then don't process the test until we see a stop
      
      if( test_waiting_for_stop || ((++test_loop_count) <= TEST_EVERY_N_LOOPS) )
	{
	  // Wait another loop before running test
	}
      else
	{
	  test_loop_count = 0;
	  
	  if( test_running )
	    {
	      // Initialise?
	      if( test_done_init )
		{
		  // Init done, queue token
		  TOKEN t = tests[test_number].seq[test_step];

		  int rn = -1;
		  int test_type = TC_END;		  
		  int done = 0;

#if DUMP_STATE_STAGE_C
                  cli_dump_state();
#endif

#if DEBUG_TEST_SEQ
		  printf("\n  Token:%d", t);
#endif
		  switch(t)
		    {
		    case TOK_TEST_WAIT_FOR_STOP:

		      // Wait and run in one operation so the program doesn't run and end before we are waiting for it
		      // to stop
		      
		      test_waiting_for_stop = 1;
		      s->run = 1;

		      // Skip past this code
		      test_step++;
#if DEBUG_TEST_SEQ
		      printf("\n  TOK_TEST_WAIT_FOR_STOP  test_waiting_for_stop:%d", test_waiting_for_stop);
#endif
		      break;
		      
		    case TOK_NONE:
		    case TOK_TEST_CHECK_RES:
		      
		      // Test sequence finished
		      // Test results

		      // This test is not waiting for a stop any more
		      test_waiting_for_stop = 0;

#if DEBUG_TEST_SEQ                      
		      printf("\n  Checking results  test_waiting_for_stop:%d", test_waiting_for_stop);
				      
		      printf("\nChecking results for test: %s", tests[test_number].desc);
#endif
		      // Which type of test do we do?
		      test_type = TC_END;
			  
		      while(!done)
			{
#if DEBUG_TEST_SEQ
			  printf("\n  Test_res_i:%d TC code:%d", test_res_i, t);
#endif
			  switch(tests[test_number].result_codes[test_res_i].code)
			    {
			    case TC_STORE_N:
			      test_type = TC_STORE_N;
			      rn = tests[test_number].result_codes[test_res_i].n;
#if DEBUG_VERBOSE_TEST
			      printf("\nTesting store[%04X]", rn);
#endif
			      break;

			    case TC_REG_N:
			      test_type = TC_REG_N;
			      rn = tests[test_number].result_codes[test_res_i].n;
#if DEBUG_VERBOSE_TEST
			      printf("\nTesting R[%d]", rn);
#endif
			      break;

			    case TC_REG_IAR:
                            case TC_REG_LINK:
			    case TC_REG_KI:
			    case TC_REG_ADDR:
			    case TC_CL:

			      rn = tests[test_number].result_codes[test_res_i].code;
#if DEBUG_TEST_SEQ
			      printf("\n  TC_REG_xxx:%d rn=%d", t, rn);
#endif
			      break;

			    case TC_MUST_BE_STOPPED:
#if DEBUG_TEST_SEQ
                              printf("\nTesting for stopped. Stop = %d Run=%d", s->stop, s->run);
#endif
			      if( s->stop )
				{
				  // Stop is set, all ok
				}
			      else
				{
				  test_fail_info("Stop = 0");
				  tests[test_number].passed = 0;
				}
			      break;

			    case TC_MUST_BE_NOT_STOPPED:
#if DEBUG_TEST_SEQ
                              printf("\nTesting for not stopped. Stop = %d Run=%d", s->stop, s->run);
#endif
			      if( !s->stop )
				{
				  // Stop is not set, all ok
				}
			      else
				{
				  test_fail_info("Stop = 1");
				  tests[test_number].passed = 0;
				}
			      break;
			      
			    case TC_MUST_BE:
#if DEBUG_TEST_SEQ
			      printf("\nTest type: %s", tc_reg_name(test_type));
#endif
			      switch(test_type)
				{
				  // Test against the store
				case TC_STORE_N:
				  if( load_from_store(s, rn) == tests[test_number].result_codes[test_res_i].n )
				    {
#if DEBUG_TEST_SEQ
				      printf("\nStore[%02X] (%08X) == %016llX", rn, load_from_store(s, rn), tests[test_number].result_codes[test_res_i].n);
#endif
				    }
				  else
				    {
#if DEBUG_TEST_SEQ
				      // Not OK
				      printf("\nStore[%02X] (%08X) <> %016llX", rn, load_from_store(s, rn), tests[test_number].result_codes[test_res_i].n);
#endif
				      test_fail_info("Store[%02X] (%08X) <> %016llX", rn, load_from_store(s, rn), tests[test_number].result_codes[test_res_i].n);
				      tests[test_number].passed = 0;
				    }
				  break;

				  // Test against a register
				case TC_END:
				case TC_REG_N:
				  if( rn != -1 )
				    {
				      switch(rn)
					{
					case TC_REG_N:
					case TC_STORE_N:
					case TC_MUST_BE:
					case TC_END:
					  printf("\nTest code %d used as register index compare");
					  break;
					  
					case TC_REG_IAR:
                                        case TC_REG_LINK:
					case TC_REG_KI:
					case TC_REG_ADDR:
					case TC_CL:
					default:
					  if( read_any_size_register(s, rn) == tests[test_number].result_codes[test_res_i].n )
					    {
#if DEBUG_TEST_SEQ
					      // All OK
					      printf("\nR[%d] == %08xd, OK", rn, tests[test_number].result_codes[test_res_i].n);
#endif
					    }
					  else
					    {
#if DEBUG_TEST_SEQ
					      // Not OK
					      printf("\nR[%d] <> %016llx", rn, tests[test_number].result_codes[test_res_i].n);
#endif
					      test_fail_info("R[%s] (%016llx) <> %016llx", tc_reg_name(rn), read_any_size_register(s, rn), tests[test_number].result_codes[test_res_i].n);
					      
					      tests[test_number].passed = 0;
					    }
					  break;
					}
				      break;
				    }
				  break;
				}
			      test_type = TC_END;
			      break;
			      
			    case TC_END_SECTION:
			      // All ok, we aren't done yet, keep going
#if DEBUG_TEST_SEQ
			      printf("\nTC_END_SECTION");

#endif
			      // Skip the end section code
			      test_step++;
			      done = 1;			      
			      break;
			      
			    case TC_END:
#if DEBUG_TEST_SEQ
			      printf("\nResult check done\n");
#endif
			      done = 1;
			      test_running = 0;
			      test_waiting_for_stop = 0;
			      
			      // Reset result pointer ready for next test
			      test_res_i = 0;
			      break;
			  
			    default:
#if DEBUG_TEST_SEQ
			      printf("\nUnknown test TC code (test %d, i=%d, code=%d)", test_number, test_res_i, tests[test_number].result_codes[test_res_i].code);
#endif
			      test_running = 0;
			      done = 1;
			      break;
			    }
		      
			  test_res_i++;
			}

		      // Test has run, see if we should run another, or stop
		      // If we have checked results due to a section end then continue running the test
		      if( test_running )
			{
#if DEBUG_TEST_SEQ
			  printf("\nTC_SECTION_END so continuing...");
#endif
			}
		      else
			{
			  if( !test_run_single_test )
			    {
			      // Copy fail text, if test failed
			      if( !tests[test_number].passed )
				{
				  strcpy(tests[test_number].fail_text, test_fail_buffer);
				}

#if DEBUG_VERBOSE_TEST
			      printf("\nMoving to next test...");
#endif	      
			      // Move to next test if there is one
			      test_number++;
			      clear_test_fail_buffer();
			      
			      if( strcmp( tests[test_number].desc, "--END--") != 0 )
				{
				  
				  test_run_single_test = 0;
				  test_running   = 1;
				  test_done_init = 0;
				}
			      else
				{
				  // End of tests, stop
				  test_running = 0;
				  
				  printf("\nTest END marker found, stopping tests...");
				}
			    }
			  else
			    {
			      // Copy fail text, if test failed
			      if( !tests[test_number].passed )
				{
				  strcpy(tests[test_number].fail_text, test_fail_buffer);
				}
			    }
			} 
		      break;
		      
		    default:
#if DEBUG_TEST_SEQ
		      printf("\n Queuing token %d\n", t);
#endif
		      queue_token(t);
		      test_step++;
		      break;
		    }
		}
	      else
		{
		  // Init not done, do it
		  int i = 0;
		  int rn = 0;
		  int done = 0;

#if DEBUG_VERBOSE_TEST
		  printf("\n================================================");
		  printf("\nInitialising test: %s", tests[test_number].desc);
		  printf("\n================================================");
#endif
		  test_res_i = 0;
		  
		  load_store_from_test(s, test_number);
		  
		  while(!done)
		    {
		      switch(tests[test_number].init_codes[i].code)
			{
			case IC_SET_REG_N:
			  rn = tests[test_number].init_codes[i].n;
			  break;

			case IC_SET_REG_V:
			  register_assign_register_uint64(s, rn, tests[test_number].init_codes[i].n );
			  break;
		      
			case IC_END:
			  done = 1;
			  test_done_init = 1;

			  // Set up test sequence step number
			  test_step = 0;
			  break;
		      
			default:
			  printf("\nUnknown test IC code (test %d, i=%d)", test_number, i);
			  test_running = 0;
			  break;
			}

		      i++;
		    }
		}
	    }
	}
    }

#if ESC_TYPE_SMALL  
  // On last drive, process the scan
  if(kbd_drv_i == (NUM_KBD_DRV - 1))
    {
      // Copy scan code over
      kbd_output_scan_code = kbd_scan_code;

      // If scan code is different to the last scan code then if it is non zero,
      // inject a keycode into the main FSM
      if( (kbd_last_output_scan_code != kbd_output_scan_code) && (kbd_output_scan_code != 0) )
	{
#if DEBUG_KEY_SCAN
	  printf("\nKeyscan code :%03X", kbd_output_scan_code);
#endif
	  kbd_queue_key(kbd_output_scan_code);
	}

      kbd_last_output_scan_code = kbd_output_scan_code;
    }

#endif
  
}

#if ESC_TYPE_SMALL

void kbd_debounce(void)
{
  // Key pressed?
  if( kbd_scan_code == 0 )
    {
      // No key pressed now
      // Count down
      if( kbd_db_count > 0 )
	{
	  kbd_db_count--;
	}
    }
  else
    {
      // Key pressed now
      // If same key pressed as last scan then count up, else count down
      if( kbd_scan_code == kbd_last_scan_code )
	{
	  if( kbd_db_count < KBD_DB_COUNT_MAX )
	    {
	      kbd_db_count++;
	    }
	}
      else
	{
	  if( kbd_db_count > 0 )
	    {
	      kbd_db_count--;
	    }
	}
    }
}



void kbd_scan(ESC_STATE *s)
{
  kbd_t_slot = (kbd_t_slot + 1 ) % NUM_KBD_T_SLOTS;

  switch(kbd_t_slot)
    {
    case 1:
      kbd_drive();
      break;

    case 9:
      kbd_read(s);      
      break;
    }
}

#endif

////////////////////////////////////////////////////////////////////////////////
//
//
//

// The computer instance

ESC_STATE esc_state;

// Display
#define MAX_DSP   ((MAX_LINE+1)*NUM_LINES)

char dsp[1000];

char *get_display(void)
{
  return(dsp);
}


////////////////////////////////////////////////////////////////////////////////
//
// Read any register
//
// Always returns a double word as it could be a double word register
//

REGISTER_DOUBLE_WORD read_any_size_register(ESC_STATE *s, int n)
{
  if( n == TC_REG_IAR )
    {
      return((REGISTER_DOUBLE_WORD)s->iar.address);
    }

  if( n == TC_REG_LINK )
    {
      return((REGISTER_DOUBLE_WORD)s->link_register);
    }

  if( n == TC_REG_KI )
    {
      return((REGISTER_DOUBLE_WORD)s->keyboard_register);
    }

  if( n == TC_REG_ADDR )
    {
      return((REGISTER_DOUBLE_WORD)s->address_register);
    }

  if( n == TC_CL )
    {
      return(s->control_latch);
    }
  
  if( IS_SW_REGISTER(n) )
    {
      //      return((REGISTER_DOUBLE_WORD)SW_REG_CONTENTS(n));
      return(read_register(s, n));
    }

  if( IS_DW_REGISTER(n) )
    {
      //return((REGISTER_DOUBLE_WORD)DW_REG_CONTENTS(n));
      return(read_register(s, n));
    }

  error_msg("Unrecognised register:R%d", n);
}

////////////////////////////////////////////////////////////////////////////////
//
// Read any register and return absolute value
//

REGISTER_DOUBLE_WORD read_any_size_register_absolute(ESC_STATE *s, int n)
{
  if( IS_SW_REGISTER(n) )
    {
      //      return(REMOVED_SW_SIGN((REGISTER_DOUBLE_WORD)SW_REG_CONTENTS(n)));
      return(REMOVED_SW_SIGN(read_register(s, n)));
    }

  if( IS_DW_REGISTER(n) )
    {
      return(REMOVED_DW_SIGN(read_register(s,n)));
    }

  error_msg("Unrecognised register:R%d", n);
}

////////////////////////////////////////////////////////////////////////////////
//
// BCD
//
//
// Normalise a value after a binary addition
//
//

REGISTER_SINGLE_WORD single_sum_normalise(REGISTER_SINGLE_WORD v)
{
#if DEBUG_BCD_CORRECTION
  printf("\nValue:%08X", v);
#endif
  
  // Add 6 to each non-bcd digit
  for(int i=0; i<sizeof(REGISTER_SINGLE_WORD)*8; i+=4)
    {
      // get digit value
      int digit = ((v & (0xF << i)) >> i);

#if DEBUG_BCD_CORRECTION
      printf("\nDigit test:%d", digit);
#endif
      // Add 6 if not bcd
      switch(digit)
	{
	case 10:
	case 11:
	case 12:
	case 13:
	case 14:
	case 15:
	  v += (0x6<<i);
	  printf("\n  Added 6:%08X", v);
	  break;
	}
    }

#if DEBUG_BCD_CORRECTION
  printf("\nValue:%08X", v);
#endif

  return(v);
}


REGISTER_DOUBLE_WORD double_sum_normalise(REGISTER_DOUBLE_WORD v)
{
#if DEBUG_BCD_CORRECTION
  printf("\n%s: Value:%016llX", __FUNCTION__, v);
#endif
  
  // Add 6 to each non-bcd digit
  for(int i=0; i<sizeof(REGISTER_DOUBLE_WORD)*8; i+=4)
    {
      // Get digit value
      REGISTER_DOUBLE_WORD digit = ((v & (0xFL << i)) >> i);

#if DEBUG_BCD_CORRECTION
      printf("\nDigit test:%d", digit);
#endif
      // Add 6 if not bcd
      switch(digit)
	{
	case 10:
	case 11:
	case 12:
	case 13:
	case 14:
	case 15:
	  v += (0x6L<<i);
	  printf("\n  Added 6:%016llX", v);
	  break;
	}
    }

#if DEBUG_BCD_CORRECTION
  printf("\nValue:%016llX", v);
#endif

  return(v);
}

////////////////////////////////////////////////////////////////////////////////
//
// Ensure signs are tagged
// If there's no explicit plus then change it

int fix_sign(int sign)
{
  switch(sign)
    {
    case WORD_SIGN_MINUS:
    case WORD_SIGN_PLUS:
      break;
      
    default:
      sign = WORD_SIGN_PLUS;
      break;
    }
  return(sign);
}

////////////////////////////////////////////////////////////////////////////////
//
// Nines complement
//

REGISTER_SINGLE_WORD bcd_sw_nines_complement(REGISTER_SINGLE_WORD n)
{
  return(0x00999999 - n);
}

REGISTER_DOUBLE_WORD bcd_dw_nines_complement(REGISTER_DOUBLE_WORD n)
{
  return(0x0000999999999999L - n);
}

////////////////////////////////////////////////////////////////////////////////

// Get sign from any size register

int any_size_sign(ESC_STATE *s, int regno)
{
  if( IS_SW_REGISTER(regno) )
    {
      //      return( SW_SIGN(SW_REG_CONTENTS(regno)) );
      return( SW_SIGN(read_register(s, regno)) );
    }

  if( IS_DW_REGISTER(regno) )
    {
      //      return( DW_SIGN(DW_REG_CONTENTS(regno)) );
      return( DW_SIGN(read_register(s, regno)) );
    }

  error_msg("Unrecognised register:R%d", regno);
}

void set_any_size_sign(ESC_STATE *s, int regno, int sign)
{
  if( IS_SW_REGISTER(regno) )
    {
      //SW_REG_CONTENTS(regno) = SET_SW_SIGN(s->R[regno], sign);
      write_register(s, regno, SET_SW_SIGN(read_register(s, regno), sign));
      return;
    }

  if( IS_DW_REGISTER(regno) )
    {
      //DW_REG_CONTENTS(regno) = SET_DW_SIGN(s->RD[regno-8], sign);
      write_register(s, regno, SET_DW_SIGN(read_register(s, regno), sign));
      return;
    }

  error_msg("Unrecognised register:R%d", regno);
}

void set_any_size_rh6(ESC_STATE *s, int regno, int rh6)
{
  REGISTER_DOUBLE_WORD reg_contents = read_register(s, regno);
  
  if( IS_SW_REGISTER(regno) )
    {
      //      int reg_contents = SW_REG_CONTENTS(regno);
      //      SW_REG_CONTENTS(regno) = (reg_contents & 0xF0000000) | rh6;
      write_register(s, regno, (reg_contents & 0xFF000000) | rh6);
      return;
    }

  if( IS_DW_REGISTER(regno) )
    {
      //int reg_contents = DW_REG_CONTENTS(regno);
      //      int reg_contents = (REGISTER_SINGLE_WORD)read_register(s, regno);
      //DW_REG_CONTENTS(regno) = (reg_contents & 0xF000000000000000) | rh6;
      write_register(s, regno, (reg_contents & 0xFFFFFFFFFF000000) | rh6);
      return;
    }

  error_msg("Unrecognised register:R%d", regno);

}

//------------------------------------------------------------------------------
//
// Get and set the RH 6 digits of any size register
//

#if 0
SINGLE_WORD any_size_rh6(ESC_STATE *s, int regno)
{
  if( IS_SW_REGISTER(regno) )
    {
      int reg_contents = SW_REG_CONTENTS(regno);
      reg_contents &= 0x00FFFFFF;      

      //printf("\nRH6 of %d is %08X", regno, reg_contents);
      return(reg_contents);
    }

  if( IS_DW_REGISTER(regno) )
    {
      DOUBLE_WORD reg_contents = DW_REG_CONTENTS(regno);
      reg_contents &= 0x00FFFFFF;      
      //      DW_REG_CONTENTS(regno) = sign;
      return((SINGLE_WORD)reg_contents);
    }

  error_msg("Unrecognised register:R%d", regno);
}
#else

SINGLE_WORD any_size_rh6(ESC_STATE *s, int regno)
{
  REGISTER_DOUBLE_WORD reg_contents = read_register(s, regno);

  reg_contents &= 0x00FFFFFF;      
  //      DW_REG_CONTENTS(regno) = sign;
  return((SINGLE_WORD)reg_contents);
}

#endif

//------------------------------------------------------------------------------

REGISTER_SINGLE_WORD invert_sw_sign(REGISTER_SINGLE_WORD n)
{
  REGISTER_SINGLE_WORD r = n;
  
  if( SW_SIGN(n) == WORD_SIGN_PLUS)
    {
      r = SET_SW_SIGN(r, WORD_SIGN_MINUS);
    }

  if( SW_SIGN(n) == WORD_SIGN_MINUS)
    {
      r = SET_SW_SIGN(r, WORD_SIGN_PLUS);
    }
  
  return(r);
}

REGISTER_DOUBLE_WORD invert_dw_sign(REGISTER_DOUBLE_WORD n)
{
  REGISTER_DOUBLE_WORD r = n;
  
  if( DW_SIGN(n) == WORD_SIGN_PLUS)
    {
      r = SET_DW_SIGN(r, WORD_SIGN_MINUS);
    }

  if( DW_SIGN(n) == WORD_SIGN_MINUS)
    {
      r = SET_DW_SIGN(r, WORD_SIGN_PLUS);
    }
  
  return(r);
}

////////////////////////////////////////////////////////////////////////////////
//
// 24 bits BCD addition, positive only (no sign digit or exponent)
// 
//
////////////////////////////////////////////////////////////////////////////////

// Plain BCD addition

REGISTER_SINGLE_WORD bcd_addition_single(REGISTER_SINGLE_WORD a, REGISTER_SINGLE_WORD b)
{
  REGISTER_SINGLE_WORD c = 0;
  
  // Add each digit, testing for digit >=10 and also propagating carry to next digit
  //
  // Add 6 to each non-bcd digit

  int carry = 0;
  
  for(int i=0; i<sizeof(REGISTER_SINGLE_WORD)*8; i+=4)
    {
      // Get digit value
      int a_digit = ((a & (0xF << i)) >> i);
      int b_digit = ((b & (0xF << i)) >> i);
      int c_digit = a_digit + b_digit + carry;
      carry = 0;
      
#if DEBUG_BCD_CORRECTION
      printf("\n%s: Add: a:%d + b:%d = %d", __FUNCTION__, a_digit, b_digit, c_digit);
#endif
      // Add 6 if not bcd, we may need to propagate a carry (9+9 = 18, so 6 is added and 24 results
      // which is 0x18)
      
      switch(c_digit)
	{
	case 10:
	case 11:
	case 12:
	case 13:
	case 14:
	case 15:
	case 16:
	case 17:
	case 18:
	case 19:
	  // Add 6, then propagate a carry
	  c_digit = (c_digit + 6) % 16;
	  carry = 1;
	  break;
	}

      // Build c, a digit at a time
      c += (c_digit << i);

#if DEBUG_BCD_CORRECTION
      printf("\n%s: Result so far: %08X", __FUNCTION__, c);
#endif

    }

  // Mask out the top two digits as there is probably an overflow from a nines-complement addition
  c &= 0x00FFFFFF;
  
#if DEBUG_BCD_CORRECTION
  printf("\n%s: Result: %08X", __FUNCTION__, c);
#endif
  
  return(c);
  
}


REGISTER_DOUBLE_WORD bcd_addition_double(REGISTER_DOUBLE_WORD a, REGISTER_DOUBLE_WORD b)
{
  REGISTER_DOUBLE_WORD c = 0;
  
  // Add each digit, testing for digit >=10 and also propagating carry to next digit
  //
  // Add 6 to each non-bcd digit

  int carry = 0;
  REGISTER_DOUBLE_WORD mask;
  
  for(int i=0; i<sizeof(REGISTER_DOUBLE_WORD)*8; i+=4)
    {
      mask = (REGISTER_DOUBLE_WORD)0xFL << i;
      
      // Get digit value
      REGISTER_DOUBLE_WORD a_digit = ((a & mask) >> i);
      REGISTER_DOUBLE_WORD b_digit = ((b & mask) >> i);
      REGISTER_DOUBLE_WORD c_digit = a_digit + b_digit + carry;
      carry = 0;
      
#if DEBUG_BCD_CORRECTION

      printf("\n%s: Add: a:%016llX + b:%016llX = %lld", __FUNCTION__, a_digit, b_digit, c_digit);
      printf("\na:%016llX a(2):%016llX a(3):%016llX", a, a & (0xFL <<i), mask);
#endif
      // Add 6 if not bcd, we may need to propagate a carry (9+9 = 18, so 6 is added and 24 results
      // which is 0x18)
      
      switch(c_digit)
	{
	case 10:
	case 11:
	case 12:
	case 13:
	case 14:
	case 15:
	case 16:
	case 17:
	case 18:
	case 19:
	  // Add 6, then propagate a carry
	  c_digit = (c_digit + 6L) % 16L;
	  carry = 1;
	  break;
	}

      // Build c, a digit at a time
      c += (c_digit << i);

#if DEBUG_BCD_CORRECTION
      printf("\n%s: Result so far: %08X", __FUNCTION__, c);
#endif

    }

  // Mask out the top two digits as there is probably an overflow from a nines-complement addition
  c &= 0x0000FFFFFFFFFFFFL;
  
#if DEBUG_BCD_CORRECTION
  printf("\n%s: Result: %016llX", __FUNCTION__, c);
#endif
  
  return(c);
  
}

////////////////////////////////////////////////////////////////////////////////
// BCD single word addition
// Signed
//
// Both positive: Add, check for overflow
// Both negative: Add, check for overflow
// One negative, one positive: Nines complement negative, add, drop carry, add one, check for overflow (inverted)

REGISTER_SINGLE_WORD bcd_sw_addition(ESC_STATE *s, REGISTER_SINGLE_WORD a, REGISTER_SINGLE_WORD b)
{
  REGISTER_SINGLE_WORD c;
  int a_sign;
  int b_sign;

#if DEBUG_SW_BCD_SUM
  printf("\n--------------------------------");
  printf("\n%s:a=%08X  b=%08X", __FUNCTION__, a, b);
#endif
  
  // Remove and save the signs

  a_sign = SW_SIGN(a);
  b_sign = SW_SIGN(b);

  switch(a_sign)
    {
    case WORD_SIGN_MINUS:
    case WORD_SIGN_PLUS:
      break;
      
    default:
      a_sign = WORD_SIGN_PLUS;
      break;
    }

  switch(b_sign)
    {
    case WORD_SIGN_MINUS:
    case WORD_SIGN_PLUS:
      break;
      
    default:
      b_sign = WORD_SIGN_PLUS;
      break;
    }
  
#if DEBUG_SW_BCD_SUM
  printf("\nasgn=%d  bsgn=%d", a_sign, b_sign);
#endif

  a = REMOVED_SW_SIGN(a);
  b = REMOVED_SW_SIGN(b);

  // If signs are different then we need to work out what the sign of the result is
  int res_sign;
  
  if( a > b )
    {
      res_sign = a_sign;
    }
  else
    {
      res_sign = b_sign;
    }

#if DEBUG_SW_BCD_SUM
  printf("\na(rs)=%08X  b(rs)=%08X result sign:%d", a, b, res_sign);
#endif

  // If both numbers are positive or both are negative the just add the digits
  if( ((a_sign == WORD_SIGN_MINUS) && (b_sign == WORD_SIGN_MINUS)) ||
      ((a_sign == WORD_SIGN_PLUS) && (b_sign == WORD_SIGN_PLUS)) )
    {
#if DEBUG_SW_BCD_SUM
      printf("\nSigns identical");
#endif

      c = bcd_addition_single(a, b);

#if DEBUG_SW_BCD_SUM
      printf("\nc=%08X", c);
#endif

      c = single_sum_normalise(c);

#if DEBUG_SW_BCD_SUM
      printf("\nc=%08X", c);
#endif
      
      if( OVERFLOW_SW(c) )
	{
#if DEBUG_SW_BCD_SUM
	  printf("\nOverflow occurred");

	  error_msg( "Overflow (%08X)", c);
	  s->error = 1;
	  s->stop= 1;
#endif
	}

      // Signs are unchanged
      c = SET_SW_SIGN(c, a_sign);
      return(c);
    }

  // If we get here then the signs of the numbers are different
  // If number negative then use tens complemet
#if DEBUG_SW_BCD_SUM
  printf("\nSigns different");
#endif

  if( a_sign == WORD_SIGN_MINUS )
    {
      a = bcd_sw_nines_complement(a);
    }

  if( b_sign == WORD_SIGN_MINUS )
    {
      b = bcd_sw_nines_complement(b);
    }

#if DEBUG_SW_BCD_SUM
  printf("\n%s:a=%08X  b=%08X", __FUNCTION__, a, b);
#endif
  
#if DEBUG_SW_BCD_SUM
  printf("\nSigns different");
#endif

  c = bcd_addition_single(a, b);
  
  c = single_sum_normalise(c);
      
#if DEBUG_SW_BCD_SUM
  printf("\nc=%08X", c);
#endif


  // Overflow condition is reversed
  if( !OVERFLOW_SW(c) )
    {
#if DEBUG_SW_BCD_SUM
      printf("\nOverflow occurred");
#endif

      error_msg("Overflow (%08X)", c);
    }

  // Drop the carry
  c = CLEAR_SW_CARRY(c);

  // Add one
  c = bcd_addition_single(c, 1);
  
  c = single_sum_normalise(c);
  
  // If result is negative then nines complement it and add one as we use sign plus digits form for numbers
  // This format matches the floating point format
  if( res_sign == WORD_SIGN_MINUS )
    {
      c = bcd_sw_nines_complement(c);
      c = bcd_addition_single(c, 1);
      c = single_sum_normalise(c);
    }
  
  // The sign of the result will be that of the largest argument absoulte value
  c = SET_SW_SIGN(c, res_sign);
    
#if DEBUG_SW_BCD_SUM
  printf("\nc=%08X (9c:%08X)", c, bcd_sw_nines_complement(c));
#endif
  
  return(c);
}

////////////////////////////////////////////////////////////////////////////////
//
// BCD double word integer addition
//
// Signed
//
// Both positive: Add, check for overflow
// Both negative: Add, check for overflow
// One negative, one positive: Nines complement negative, add, drop carry, add one, check for overflow (inverted)

REGISTER_DOUBLE_WORD bcd_dw_addition(REGISTER_DOUBLE_WORD a, REGISTER_DOUBLE_WORD b)
{
  REGISTER_DOUBLE_WORD c;
  int a_sign;
  int b_sign;

#if DEBUG_DW_BCD_SUM
  printf("\n--------------------------------");
  printf("\n%s:a=%016llX  b=%016llX", __FUNCTION__, a, b);
#endif
  
  // Remove and save the signs
  a_sign = DW_SIGN(a);
  b_sign = DW_SIGN(b);

  a_sign = fix_sign(a_sign);
  b_sign = fix_sign(b_sign);
  
#if DEBUG_DW_BCD_SUM
  printf("\nasgn=%d  bsgn=%d", a_sign, b_sign);
#endif

  a = REMOVED_DW_SIGN(a);
  b = REMOVED_DW_SIGN(b);

  // If signs are different then we need to work out what the sign of the result is
  int res_sign;
  
  if( a > b )
    {
      res_sign = a_sign;
    }
  else
    {
      res_sign = b_sign;
    }

#if DEBUG_DW_BCD_SUM
  printf("\na(rs)=%016llX  b(rs)=%016llX result sign:%d", a, b, res_sign);
#endif

  // If both numbers are positive or both are negative the just add the digits
  if( ((a_sign == WORD_SIGN_MINUS) && (b_sign == WORD_SIGN_MINUS)) ||
      ((a_sign == WORD_SIGN_PLUS) && (b_sign == WORD_SIGN_PLUS)) )
    {
#if DEBUG_DW_BCD_SUM
      printf("\nSigns identical");
#endif

      c = bcd_addition_double(a, b);

#if DEBUG_DW_BCD_SUM
      printf("\nc=%016llX", c);
#endif

      c = double_sum_normalise(c);

#if DEBUG_DW_BCD_SUM
      printf("\nc=%016llX", c);
#endif
      
      if( OVERFLOW_DW(c) )
	{
#if DEBUG_DW_BCD_SUM
	  printf("\nOverflow occurred");

	  error_msg( "Overflow (%08X)", c);
#endif
	}

      // Signs are unchanged
      c = SET_DW_SIGN(c, a_sign);
      return(c);
    }

  // If we get here then the signs of the numbers are different
  // If number negative then use tens complemet
#if DEBUG_DW_BCD_SUM
  printf("\nSigns different result sign:%d", res_sign);
#endif

  if( a_sign == WORD_SIGN_MINUS )
    {
      a = bcd_dw_nines_complement(a);
    }

  if( b_sign == WORD_SIGN_MINUS )
    {
      b = bcd_dw_nines_complement(b);
    }

#if DEBUG_DW_BCD_SUM
  printf("\n%s:a=%016llX  b=%016llX", __FUNCTION__, a, b);
#endif
  
#if DEBUG_DW_BCD_SUM
  printf("\nSigns different");
#endif

  c = bcd_addition_double(a, b);
  
  c = double_sum_normalise(c);
      
#if DEBUG_DW_BCD_SUM
  printf("\nc=%016llX", c);
#endif


  // Overflow condition is reversed
  if( !OVERFLOW_DW(c) )
    {
#if DEBUG_DW_BCD_SUM
      printf("\nOverflow occurred");
#endif

      error_msg("Overflow (%08X)", c);
    }

  // Drop the carry
  c = CLEAR_DW_CARRY(c);

  // Add one
  c = bcd_addition_double(c, 1);
  
  c = double_sum_normalise(c);
  
  // If result is negative then nines complement it and add one as we use sign plus digits form for numbers
  // This format matches the floating point format
  if( res_sign == WORD_SIGN_MINUS )
    {
#if DEBUG_DW_BCD_SUM
      printf("res_sign is negative");
#endif
      
      c = bcd_dw_nines_complement(c);
      c = bcd_addition_double(c, 1);
      c = double_sum_normalise(c);
    }
  
  // The sign of the result will be that of the largest argument absoulte value
  c = SET_DW_SIGN(c, res_sign);
    
#if DEBUG_DW_BCD_SUM
  printf("\nc=%016llX (9c:%016llX)", c, bcd_sw_nines_complement(c));
#endif
  
  return(c);
}

////////////////////////////////////////////////////////////////////////////////
//
// Convert store value to an address.
// Addresses have no sign or exponent
//
////////////////////////////////////////////////////////////////////////////////

ADDRESS convert_store_to_address(SINGLE_WORD store_value)
{
  return(BOUND_ADDRESS(REMOVED_SW_SIGN(BOUND_ADDRESS(store_value))));
}

////////////////////////////////////////////////////////////////////////////////
//
// Convert BCD to binary
//

int bcd_to_binary(SINGLE_WORD bcd)
{
  char line[50];
  int binary;

#if DEBUG_BCD_TO_BINARY
  printf("\n%s: BCD:%X", __FUNCTION__, bcd);
#endif
  
  sprintf(line, "%X", bcd);
  sscanf(line, "%d", &binary);

#if DEBUG_BCD_TO_BINARY
  printf(" Bin1:%d", binary);
#endif

  // Limit to 200 as a store address
  if( binary < 0 )
    {
      binary = 0;
    }

  if( binary >199 )
    {
      binary = 199;
    }

#if DEBUG_BCD_TO_BINARY
  printf(" Bin2:%d", binary);
#endif
  
  
  return(binary);
}

////////////////////////////////////////////////////////////////////////////////

// Address is signed so has to have that stripped. It is never negative.
//
// It is also in BCD so has to be converted to binary to get an array index
// for the store array
//
SINGLE_WORD load_from_store(ESC_STATE *s, ADDRESS address)
{
  int idx = 0;
  SINGLE_WORD retval = 0;
  
  idx = bcd_to_binary(REMOVED_SW_SIGN(address));
  retval = s->store[idx];
  
#if DEBUG_LOAD_FROM_STORE
  printf("\n%s:address:%04X idx:%d retval=%08X", __FUNCTION__, address, idx, retval);
#endif

  return(retval);
}

void write_sw_to_store(ESC_STATE *s, ADDRESS address, REGISTER_SINGLE_WORD d)
{
  s->store[bcd_to_binary(REMOVED_SW_SIGN(address))] = d;
}

#if 0
REGISTER_DOUBLE_WORD get_register(ESC_STATE *s, int reg)
{
  return((REGISTER_DOUBLE_WORD)s->R[reg]);
}
#endif

////////////////////////////////////////////////////////////////////////////////
//
// Various register assignments
//

void register_assign_register(ESC_STATE *s, int dest, int src)
{
#if DEBUG_REG_ASSIGN
  printf("\n%s:dest:%d src:%d", __FUNCTION__, dest, src);
#endif
  
  if( IS_SW_REGISTER(dest) && IS_SW_REGISTER(src) )
    {
#if DEBUG_REG_ASSIGN
      printf("\nSW REG, SW REG");
#endif
      write_register(s, dest, read_register(s, src));
      //SW_REG_CONTENTS(dest) = SW_REG_CONTENTS(src);
    }
  
  if( IS_DW_REGISTER(dest) && IS_DW_REGISTER(src) )
    {
#if DEBUG_REG_ASSIGN
      printf("\nDOUBLE WORD, DOUBLE WORD");
#endif
      write_register(s, dest, read_register(s, src));
      //DW_REG_CONTENTS(dest) = DW_REG_CONTENTS(src);

#if DEBUG_REG_ASSIGN
      printf("\n%s:dest:%016llX", __FUNCTION__, read_register(s, dest));
#endif
    }

  if( IS_SW_REGISTER(dest) && IS_DW_REGISTER(src) )
    {
#if DEBUG_REG_ASSIGN
      printf("\nSINGLE WORD <= DOUBLE WORD");
#endif
      write_register(s, dest, DW_TO_SW(read_register(s, src)));
      //SW_REG_CONTENTS(dest) = DW_TO_SW(DW_REG_CONTENTS(src));

#if DEBUG_REG_ASSIGN
      printf("\n%s:dest:%016llX", __FUNCTION__, read_register(s, dest));
#endif
    }

  if( IS_DW_REGISTER(dest) && IS_SW_REGISTER(src) )
    {
#if DEBUG_REG_ASSIGN
      printf("\nSINGLE WORD <= DOUBLE WORD");
#endif
      write_register(s, dest, SW_TO_DW(read_register(s, src)));
      //DW_REG_CONTENTS(dest) = SW_TO_DW(SW_REG_CONTENTS(src));

#if DEBUG_REG_ASSIGN
      printf("\n%s:dest:%016llX", __FUNCTION__, read_register(s, dest));
#endif
    }
}

//------------------------------------------------------------------------------

void register_assign_register_literal(ESC_STATE *s, int dest,  int literal)
{
  if( IS_SW_REGISTER(dest) )
    {
      write_register(s, dest, SET_SW_SIGN((REGISTER_SINGLE_WORD) literal, WORD_SIGN_PLUS));
      //SW_REG_CONTENTS(dest) = SET_SW_SIGN((REGISTER_SINGLE_WORD) literal, WORD_SIGN_PLUS);
      
    }
  
  if( IS_DW_REGISTER(dest) )
    {
      write_register(s, dest, SET_DW_SIGN((REGISTER_DOUBLE_WORD) literal, WORD_SIGN_PLUS));
      //DW_REG_CONTENTS(dest) = (REGISTER_DOUBLE_WORD) literal;
    }
}

//------------------------------------------------------------------------------
//
// Literal is always positive.

void register_assign_sum_register_literal(ESC_STATE *s, int dest, int src, int literal)
{
#if DEBUG_REG_ASSIGN
  printf("\n%s:dest:%d src:%d lit:%d", __FUNCTION__, dest, src, literal);
#endif
  
  if( IS_SW_REGISTER(dest) )
    {
#if DEBUG_REG_ASSIGN
      printf("\nSINGLE WORD REG");
#endif

      REGISTER_SINGLE_WORD t;

      t = SET_SW_SIGN((REGISTER_SINGLE_WORD) literal, WORD_SIGN_PLUS);

      write_register(s, dest, bcd_sw_addition(s, read_register(s, src), t));
    //SW_REG_CONTENTS(dest) = bcd_sw_addition(s, SW_REG_CONTENTS(src), t);
    }
  
  if( IS_DW_REGISTER(dest) )
    {
      REGISTER_DOUBLE_WORD t;

#if DEBUG_REG_ASSIGN
      printf("\nDOUBLE WORD REG");
#endif

      t = SET_DW_SIGN((REGISTER_DOUBLE_WORD) literal, WORD_SIGN_PLUS);
      write_register(s, dest, bcd_dw_addition(read_register(s, src), t));
  //  DW_REG_CONTENTS(dest) = bcd_dw_addition(DW_REG_CONTENTS(src), t);

#if DEBUG_REG_ASSIGN
      printf("\n%s:dest:%016llX (lit):%016llX", __FUNCTION__, read_register(s, dest), t);
#endif

    }
}

//------------------------------------------------------------------------------
//
// Subtract a register from a constant
//
// Swap register sign and add
// Literal is always positive

void register_assign_sub_literal_register(ESC_STATE *s, int dest, int literal, int src)
{
  if( IS_SW_REGISTER(dest) )
    {
      REGISTER_SINGLE_WORD t;

      //      t       = SET_SW_SIGN((REGISTER_SINGLE_WORD) SW_REG_CONTENTS(src), WORD_SIGN_MINUS);
      //      t = invert_sw_sign(SW_REG_CONTENTS(src));
      t = invert_sw_sign((REGISTER_SINGLE_WORD)read_register(s, src));
      
      literal = SET_SW_SIGN((REGISTER_SINGLE_WORD) literal,   WORD_SIGN_PLUS);

      //      SW_REG_CONTENTS(dest) = bcd_sw_addition(s, (REGISTER_SINGLE_WORD) literal, t);
      write_register(s, dest, bcd_sw_addition(s, (REGISTER_SINGLE_WORD) literal, t));
    }
  
  if( IS_DW_REGISTER(dest) )
    {
      REGISTER_DOUBLE_WORD t;

      //t       = SET_DW_SIGN((REGISTER_DOUBLE_WORD) DW_REG_CONTENTS(src), WORD_SIGN_MINUS);
      //      t = invert_dw_sign(DW_REG_CONTENTS(src));
      t = invert_dw_sign(read_register(s, src));
      
      literal = SET_DW_SIGN((REGISTER_DOUBLE_WORD) literal,   WORD_SIGN_PLUS);

    //DW_REG_CONTENTS(dest) = bcd_dw_addition((REGISTER_DOUBLE_WORD) literal, t);
      write_register(s, dest, bcd_dw_addition((REGISTER_DOUBLE_WORD) literal, t));
    }
}

void register_assign_sub_register_literal(ESC_STATE *s, int dest, int src, int literal)
{
  if( IS_SW_REGISTER(dest) )
    {
      REGISTER_SINGLE_WORD t;

      t = SET_SW_SIGN((REGISTER_SINGLE_WORD) literal, WORD_SIGN_MINUS);

     // SW_REG_CONTENTS(dest) = bcd_sw_addition(s, (REGISTER_SINGLE_WORD) t, SW_REG_CONTENTS(src));
      write_register(s, dest,  bcd_sw_addition(s, (REGISTER_SINGLE_WORD) t, (REGISTER_SINGLE_WORD)read_register(s, src)));
    }
  
  if( IS_DW_REGISTER(dest) )
    {
      REGISTER_DOUBLE_WORD t;

      t = SET_DW_SIGN((REGISTER_DOUBLE_WORD) literal, WORD_SIGN_MINUS);

    // DW_REG_CONTENTS(dest) = bcd_dw_addition((REGISTER_DOUBLE_WORD) t, DW_REG_CONTENTS(src));
      write_register(s, dest,  bcd_dw_addition((REGISTER_DOUBLE_WORD) t, read_register(s, src)));
    }
}

void register_assign_sum_register_register(ESC_STATE *s, int dest, int src1, int src2)
{
  if( IS_SW_REGISTER(dest) && IS_SW_REGISTER(src1) && IS_SW_REGISTER(src2) )
    {
      //      SW_REG_CONTENTS(dest) = bcd_sw_addition(s, SW_REG_CONTENTS(src1), SW_REG_CONTENTS(src2));
      write_register(s, dest, bcd_sw_addition(s, read_register(s, src1), read_register(s, src2)));
      return;
    }

  if( IS_DW_REGISTER(dest) && IS_DW_REGISTER(src1) && IS_DW_REGISTER(src2) )
    {
      //      DW_REG_CONTENTS(dest) = bcd_dw_addition(DW_REG_CONTENTS(src1), DW_REG_CONTENTS(src2));
      write_register(s, dest, bcd_dw_addition(read_register(s, src1), read_register(s, src2)));
      return;
    }

  if( IS_DW_REGISTER(dest) && IS_DW_REGISTER(src1) && IS_SW_REGISTER(src2) )
    {
      //      DW_REG_CONTENTS(dest) = bcd_dw_addition(DW_REG_CONTENTS(src1), SW_TO_DW(SW_REG_CONTENTS(src2)));
      write_register(s, dest, bcd_dw_addition(read_register(s, src1), SW_TO_DW(read_register(s, src2))));
      return;
    }

  if( IS_SW_REGISTER(dest) && IS_SW_REGISTER(src1) && IS_DW_REGISTER(src2) )
    {
      //  SW_REG_CONTENTS(dest) = bcd_sw_addition(s, SW_REG_CONTENTS(src1), DW_TO_SW(DW_REG_CONTENTS(src2)));
      write_register(s, dest, bcd_sw_addition(s, read_register(s, src1), DW_TO_SW(read_register(s, src2))));
      return;
    }

  // error
  error_msg("Registers of different sizes");
}

////////////////////////////////////////////////////////////////////////////////

#if 0
void register_assign_sub_register_register(ESC_STATE *s, int dest, int src1, int src2)
{
#if DEBUG_REGISTER_ASSIGN
  printf("\n%s: dest:%d src1:%d src2:%d", __FUNCTION__, dest, src1, src2);
  printf("\n%s: issw:%d issw:%d issw:%d", __FUNCTION__, IS_SW_REGISTER(dest), IS_SW_REGISTER(src1), IS_SW_REGISTER(src2) );
  printf("\n%s: isdw:%d isdw:%d isdw:%d", __FUNCTION__, IS_DW_REGISTER(dest), IS_DW_REGISTER(src1), IS_DW_REGISTER(src2) );
  
#endif
  
  if( IS_SW_REGISTER(dest) && IS_SW_REGISTER(src1) && IS_SW_REGISTER(src2) )
    {
#if DEBUG_REGISTER_ASSIGN
      printf("\nSW SW SW");
#endif
      //      SW_REG_CONTENTS(dest) = bcd_sw_addition(s, SW_REG_CONTENTS(src1), invert_sw_sign( SW_REG_CONTENTS(src2)));
      write_register(s, dest, bcd_sw_addition(s, read_register(s, src1), invert_sw_sign( read_register(s, src2))));
      return;
    }

  if( IS_DW_REGISTER(dest) && IS_DW_REGISTER(src1) && IS_DW_REGISTER(src2) )
    {
#if DEBUG_REGISTER_ASSIGN
      printf("\nDW DW DW");
#endif
      //      DW_REG_CONTENTS(dest) = bcd_dw_addition(DW_REG_CONTENTS(src1), invert_dw_sign( DW_REG_CONTENTS(src2)));
      write_register(s, dest, bcd_dw_addition(read_register(s, src1), invert_dw_sign( read_register(s, src2))));
      
      return;
    }

  if( IS_DW_REGISTER(dest) && IS_DW_REGISTER(src1) && IS_SW_REGISTER(src2) )
    {
#if DEBUG_REGISTER_ASSIGN
      printf("\nDW DW SW");
#endif
      //      DW_REG_CONTENTS(dest) = bcd_dw_addition(DW_REG_CONTENTS(src1), invert_dw_sign(SW_TO_DW(SW_REG_CONTENTS(src2))));
      write_register(s, dest, bcd_dw_addition(read_register(s, src1), invert_dw_sign( SW_TO_DW(read_register(s, src2)))));
      return;
    }

  if( IS_SW_REGISTER(dest) && IS_SW_REGISTER(src1) && IS_DW_REGISTER(src2) )
    {
        
#if DEBUG_REGISTER_ASSIGN
      printf("\nSW SW DW");
#endif
      //      SW_REG_CONTENTS(dest) = bcd_sw_addition(s, SW_REG_CONTENTS(src1), invert_sw_sign(DW_TO_SW(DW_REG_CONTENTS(src2))));
      write_register(s, dest, bcd_sw_addition(s, read_register(s, src1), invert_sw_sign( DW_TO_SW(read_register(s, src2)))));
      return;
    }

  // error
  error_msg("Registers of different sizes");
}
#else
void register_assign_sub_register_register(ESC_STATE *s, int dest, int src1, int src2)
{
  int is_dest_dw = 0;
  int is_src1_dw = 0;
  int is_src2_dw = 0;

  is_dest_dw = IS_DW_REGISTER(dest);
  is_src1_dw = IS_DW_REGISTER(src1);
  is_src2_dw = IS_DW_REGISTER(src2);

  REGISTER_DOUBLE_WORD w_dest = read_register(s, dest);
  REGISTER_DOUBLE_WORD w_src1 = read_register(s, src1);
  REGISTER_DOUBLE_WORD w_src2 = read_register(s, src2);

#if DEBUG_REGISTER_ASSIGN
  printf("\n%s: dest:%d src1:%d src2:%d", __FUNCTION__, dest, src1, src2);
  printf("\n%s: isdw:%d isdw:%d isdw:%d", __FUNCTION__, is_dest_dw, is_src1_dw, is_src2_dw );
  
#endif

  // Convert SW values to DW
  if( !is_src1_dw )
    {
      w_src1 = SW_TO_DW(w_src1);
    }

  if( !is_src2_dw )
    {
      w_src2 = SW_TO_DW(w_src2);
    }

  // Perform arithmetic
  w_dest = bcd_dw_addition(w_src1, invert_dw_sign( w_src2));

  // Convert DW back to SW if needed
  if( !is_dest_dw )
    {
      w_dest = DW_TO_SW(w_dest);
    }
  
  // Write value back

#if DEBUG_REGISTER_ASSIGN
  printf("\n%s: src1:%016X", __FUNCTION__, w_src1 );
  printf("\n%s: src2:%016X", __FUNCTION__, w_src2 );
  printf("\n%s: src3:%016X", __FUNCTION__, w_dest );
  
#endif
  
  write_register(s, dest, w_dest);

}
#endif

////////////////////////////////////////////////////////////////////////////////

void register_assign_register_uint64(ESC_STATE *s, int dest, uint64_t n)
{
  if( IS_SW_REGISTER(dest) )
    {
      //      SW_REG_CONTENTS(dest) = (REGISTER_SINGLE_WORD)n;
      write_register(s, dest, n);
      return;
    }

  if( IS_DW_REGISTER(dest) )
    {
      //      DW_REG_CONTENTS(dest) = (REGISTER_DOUBLE_WORD) n;
      write_register(s, dest, n);
      return;
    }

  // error
  error_msg("Register unknown *%d), dest");
}

#if 0
#define SHIFT_INST(SHIFT_TYPE,SHIFT_OP)					\
									\
  void register_ ## SHIFT_TYPE ## _shift(ESC_STATE *s, int dest, int n)	\
  {									\
    int sign;								\
    REGISTER_SINGLE_WORD sw_data;					\
    REGISTER_DOUBLE_WORD dw_data;					\
									\
    if( IS_SW_REGISTER(dest) )						\
      {									\
	sign = SW_SIGN(SW_REG_CONTENTS(dest));				\
	sw_data = REMOVED_SW_SIGN(SW_REG_CONTENTS(dest)) SHIFT_OP (4*n); \
	sw_data = REMOVED_SW_UNUSED(sw_data);				\
	SW_REG_CONTENTS(dest) = SET_SW_SIGN(sw_data, sign);		\
	return;								\
      }									\
									\
    if( IS_DW_REGISTER(dest) )						\
      {									\
	sign = DW_SIGN(DW_REG_CONTENTS(dest));				\
	dw_data = REMOVED_DW_SIGN(DW_REG_CONTENTS(dest)) SHIFT_OP (4*n); \
	dw_data = REMOVED_DW_UNUSED(dw_data);				\
	DW_REG_CONTENTS(dest) = SET_DW_SIGN(dw_data, sign);		\
	return;								\
      }									\
									\
    error_msg("%s: Register unknown *%d", __FUNCTION__, dest);		\
  }

#else
#define SHIFT_INST(SHIFT_TYPE,SHIFT_OP)					\
									\
  void register_ ## SHIFT_TYPE ## _shift(ESC_STATE *s, int dest, int n)	\
  {									\
    int sign;								\
    REGISTER_SINGLE_WORD sw_data;					\
    REGISTER_DOUBLE_WORD dw_data;					\
									\
    if( IS_SW_REGISTER(dest) )						\
      {									\
	sign = SW_SIGN(read_register(s, dest));                          \
	sw_data = REMOVED_SW_SIGN(DW_TO_SW(read_register(s, dest))) SHIFT_OP (4*n); \
	sw_data = REMOVED_SW_UNUSED(sw_data);				\
        write_register(s, dest, SET_SW_SIGN(sw_data, sign));		\
	return;								\
      }									\
									\
    if( IS_DW_REGISTER(dest) )						\
      {									\
	sign = DW_SIGN(read_register(s, dest));                        \
	dw_data = REMOVED_DW_SIGN(read_register(s, dest)) SHIFT_OP (4*n); \
	dw_data = REMOVED_DW_UNUSED(dw_data);				\
	write_register(s, dest, SET_DW_SIGN(dw_data, sign));             \
	return;								\
      }									\
									\
    error_msg("%s: Register unknown *%d", __FUNCTION__, dest);		\
  }
#endif


SHIFT_INST(left,<<);
SHIFT_INST(right,>>);


////////////////////////////////////////////////////////////////////////////////
//
// Shift a DW right
//
// Sign is preserved
//

DOUBLE_WORD shift_dw_right(DOUBLE_WORD x)
{
  int sign = DW_SIGN(x);
  
  // Remove sign
  x = REMOVED_DW_SIGN(x);
  
  // Shift
  x >>= 4;

  // Put sign back
  x  = SET_DW_SIGN(x,  sign);

  return(x);
}

DOUBLE_WORD shift_dw_left(DOUBLE_WORD x)
{
  int sign = DW_SIGN(x);
  
  // Remove sign
  x = REMOVED_DW_SIGN(x);
  
  // Shift
  x <<= 4;

  // Put sign back
  x  = SET_DW_SIGN(x,  sign);

  return(x);
}

// Most significant digit shifted to left most position

SINGLE_WORD sw_msd_to_left(SINGLE_WORD x)
{
  SINGLE_WORD y;
  
  int sign;
  int exp;
  int digits;

  // Split the number
  sign   = STORE_GET_SIGN(x);
  exp    = STORE_GET_EXPONENT(x);
  digits = STORE_GET_DIGITS(x);

  // If exponent is 6 then we can't shift
  if( exp == 6 )
    {
      return(x);
    }
  
  // If zero then we can't do this
  if( digits == 0 )
    {
      return(x);
    }

  // Shift the digits while there's room, while updating the
  // exponent
  while( ((digits & 0x00F00000) == 0) && (exp <=4) )
    {
      digits <<=4;
      exp++;
    }

  // Rebuild the result
  y = STORE_SET_EXPONENT(y, exp);
  y = STORE_SET_SIGN(y,     sign);
  y = STORE_SET_DIGITS(y,   digits);

#if DEBUG_MSD_SHIFT
  printf("\n%s: ", __FUNCTION__);
  printf("\nx:%08X  y:%08X", x, y); 
#endif

  return(y);
}

SINGLE_WORD sw_shift_right(SINGLE_WORD x, int n)
{
  SINGLE_WORD y;
  
  int sign;
  int exp;
  int digits;

  // Split the number
  sign   = STORE_GET_SIGN(x);
  exp    = STORE_GET_EXPONENT(x);
  digits = STORE_GET_DIGITS(x);

  // If exponent is zero then we can't do this
  if( exp == 0 )
    {
      return(x);
    }
  
  // Shift the digits

  for(int i=0; i<n; i++)
    {
      digits >>=4;
      exp--;
    }

  // Rebuild the result
  y = STORE_SET_EXPONENT(y, exp);
  y = STORE_SET_SIGN(y,     sign);
  y = STORE_SET_DIGITS(y,   digits);

#if DEBUG_SW_SHIFT
  printf("\n%s: ", __FUNCTION__);
  printf("\nx:%08X  y:%08X", x, y); 
#endif

  return(y);
}

////////////////////////////////////////////////////////////////////////////////
//
// Floating point operations
//
////////////////////////////////////////////////////////////////////////////////
//
// These operations are written in a way that means that they should be
// re-writable in the instruction set of the ESC, so can be implemented
// as extracodes as the original did.
//
//------------------------------------------------------------------------------

SINGLE_WORD fp_add(ESC_STATE *s, SINGLE_WORD a, SINGLE_WORD b, int normalise)
{
  int exp_a, exp_b, exp_r;
  int exp_diff;
  int digits_a, digits_b;
  int sign_a, sign_b, sign_r;
  int digits_r;
  SINGLE_WORD result;

#if DEBUG_FP
  printf("\n%s: ", __FUNCTION__);
  printf("\na:%016X  b:%016X", a, b); 
#endif

  // trivial case
  if( STORE_GET_DIGITS(a) == 0 )
    {

#if DEBUG_FP_SUMMARY
      printf("\n%s: %s + ", __FUNCTION__, display_store_word(a));
      printf("%s = ", display_store_word(b));
      printf("%s", display_store_word(b));
#endif

      return(b);
    }

  if( STORE_GET_DIGITS(b) == 0 )
    {
#if DEBUG_FP_SUMMARY
      printf("\n%s: %s + ", __FUNCTION__, display_store_word(a));
      printf("%s = ", display_store_word(b));
      printf("%s", display_store_word(a));
#endif

      return(a);
    }
  
#if 1  
  if( normalise)
    {
      // Before we do any calculations, move the MS digit to one digit right of the left most position so we get
      // full resolution for the result and to make the test of exponents meaningful. We leave one digit to the 
      // This is done to both a and b
      
      a = sw_msd_to_left(a);
      b = sw_msd_to_left(b);
      a = sw_shift_right(a, 1);
      b = sw_shift_right(b, 1);
    }
#endif

  digits_a  =  STORE_GET_DIGITS(a);
  digits_b  =  STORE_GET_DIGITS(b);
  sign_a =  STORE_GET_SIGN(a);
  sign_b =  STORE_GET_SIGN(b);
  
  exp_a = STORE_GET_EXPONENT(a);
  exp_b = STORE_GET_EXPONENT(b);

  
  if( exp_a > exp_b )
    {
      // We shift a
      for(int i= (exp_a - exp_b); i>0; i--)
	{
	  digits_a >>= 4;
	}
      exp_r = exp_b;
      sign_r = sign_b;
    }
  else
    {
      // We shift b
      for(int i= (exp_b - exp_a); i>0; i--)
	{
	  digits_b >>= 4;
	}
      exp_r = exp_a;
      sign_r = sign_a;
    }

#if DEBUG_FP
  printf("\nexp_a:%016X  exp_b:%016X", exp_a, exp_b);
  printf("\ndigits_a:%016X  digits_b:%016X", digits_a, digits_b); 
#endif

  // Add digits
  result = bcd_sw_addition(s, SET_SW_SIGN(digits_a, sign_a), SET_SW_SIGN(digits_b,sign_b));

  // Put exponent back
  result = STORE_SET_EXPONENT(result,exp_r);

#if DEBUG_FP
  printf("\na:%s", display_store_word(a));
  printf("\nb:%s", display_store_word(b));
  printf("\nresult:%s", display_store_word(result));
  
#endif

#if DEBUG_FP_SUMMARY
  printf("\n%s: %s + ", __FUNCTION__, display_store_word(a));
  printf("%s = ", display_store_word(b));
  printf("%s", display_store_word(result));
#endif

  // Find smaller number and shift it so the exponents are the same
  return(result);
}


////////////////////////////////////////////////////////////////////////////////
//
// FP Subtract
//
////////////////////////////////////////////////////////////////////////////////

SINGLE_WORD fp_subtract(ESC_STATE *s, SINGLE_WORD a, SINGLE_WORD b, int normalise)
{
#if DEBUG_FP
  printf("\n%s: ", __FUNCTION__);
  printf("\na:%016X  b:%016X", a, b); 
#endif

  b = invert_sw_sign(b);

  return(fp_add(s, a, b, normalise));
}

////////////////////////////////////////////////////////////////////////////////
//
// FP Multiply
//
////////////////////////////////////////////////////////////////////////////////

// Uses double word registers internally

SINGLE_WORD fp_multiply(ESC_STATE *s, SINGLE_WORD a, SINGLE_WORD b)
{
  int exp_a, exp_b, exp_r;
  int exp_diff;
  int digits_a, digits_b;
  DOUBLE_WORD digits_r;
  int sign_a, sign_b, sign_r;
  SINGLE_WORD result;
  DOUBLE_WORD shifted_arg_digits;
  SINGLE_WORD tested_arg_digits;
  
  digits_a  =  STORE_GET_DIGITS(a);
  digits_b  =  STORE_GET_DIGITS(b);
  sign_a =  STORE_GET_SIGN(a);
  sign_b =  STORE_GET_SIGN(b);
  exp_a = STORE_GET_EXPONENT(a);
  exp_b = STORE_GET_EXPONENT(b);

  digits_r = 0;
  digits_r = SET_DW_SIGN(digits_r, WORD_SIGN_PLUS);
  
  // We add the smaller argument each time
  if( exp_a > exp_b )
    {
      shifted_arg_digits = digits_a;
      tested_arg_digits = digits_b;
    }
  else
    {
      shifted_arg_digits = digits_b;
      tested_arg_digits = digits_a;
    }

  // Work without sign or exponent
  shifted_arg_digits = SET_DW_SIGN(shifted_arg_digits, WORD_SIGN_PLUS);
  tested_arg_digits  = SET_SW_SIGN(tested_arg_digits,  WORD_SIGN_PLUS);
  
#if DEBUG_FP
  printf("\n%s: ", __FUNCTION__);
  printf("\na:%016X  b:%016X", a, b); 
#endif

  // We add one arg <digit> number of times then shift until all 6 digits are
  // processed.
  // Exponent then sorted out (added)
  // Sign then sorted out (xor'd)
  // Any overflow with addition => error

  for(int i=0; i<6; i++)
    {
#if DEBUG_FP
      printf("\nTested:%08X  shifted:%016llX", tested_arg_digits, shifted_arg_digits); 
#endif

      // test
      if( (tested_arg_digits & 0xF) != 0 )
        {
          for(int j=0; j<(tested_arg_digits & 0xF); j++)
            {
              digits_r = bcd_dw_addition(digits_r, shifted_arg_digits);
            }
        }
    
      // Remove sign
      shifted_arg_digits = REMOVED_DW_SIGN(shifted_arg_digits);
      tested_arg_digits  = REMOVED_SW_SIGN(tested_arg_digits);
    
      // Shift
      tested_arg_digits >>= 4;
      shifted_arg_digits <<=4;
      shifted_arg_digits = SET_DW_SIGN(shifted_arg_digits, WORD_SIGN_PLUS);
      tested_arg_digits  = SET_SW_SIGN(tested_arg_digits,  WORD_SIGN_PLUS);
    }

  
#if DEBUG_FP
  printf("\nexp_a :%016X  exp_b :%016X", exp_a, exp_b);
  printf("\nsign_a:%016X  sign_b:%016X", sign_a, sign_b);
  printf("\ndigits_a:%016X  digits_b:%016X digits_r:%016X", digits_a, digits_b, digits_r); 
#endif

  // We now need to shift the result so it will fit in a single word.
  // Shift so most significant digit is in the left most position, that will
  // give us the greatest resolution.

  exp_r = exp_a + exp_b;

#if DEBUG_FP
  printf("\nShifting to find MSD...");
  printf("\ndigits_r:%016llX exp_r:%d", digits_r, exp_r);
#endif
  
  while( ((digits_r & (DOUBLE_WORD)0x0000F00000000000L)==0) && ((digits_r & (DOUBLE_WORD)0x0000FFFFFFFFFFFFL) !=0) )
    {
      digits_r = shift_dw_left(digits_r);

      // Keep track of the number of decimal places

      exp_r++;
#if DEBUG_FP
      printf("\ndigits_r:%016llX exp_r:%d", digits_r, exp_r);
#endif
    }

#if DEBUG_FP
  printf("\nShifting done");
  printf("\ndigits_r:%016llX exp_r:%d", digits_r, exp_r);
#endif

#if DEBUG_FP
  printf("\nShifting down to fit in 6 places");
  printf("\ndigits_r:%016llX exp_r:%d", digits_r, exp_r);
#endif

  // Shift down  so the MSD is in the MS position for a single word
  // The position of the MSD was fixed above, so this is a shift of
  // a fixed number of digits.
  for(int p=0; p<6; p++)
    {
      digits_r = shift_dw_right(digits_r);

      // Keep track of the number of decimal places
      exp_r--;
    }

#if DEBUG_FP
  printf("\ndigits_r:%016llX exp_r:%d", digits_r, exp_r);
#endif
  
  // Keep result in a single word
  result = digits_r;
  
  // Put exponent back
  result = STORE_SET_EXPONENT(result, exp_r);

  // Put sign back
  if( sign_a == sign_b )
    {
      sign_r = WORD_SIGN_PLUS;
    }
  else
    {
      sign_r = WORD_SIGN_MINUS;
    }

  result = STORE_SET_SIGN(result, sign_r);
  
#if DEBUG_FP
  printf("\na:%s", display_store_word(a));
  printf("\nb:%s", display_store_word(b));
  printf("\nresult:%s", display_store_word(result));
  printf("\n%s END", __FUNCTION__);
 
#endif

#if DEBUG_FP_SUMMARY
  printf("\n%s: %s * ", __FUNCTION__, display_store_word(a));
  printf("%s = ", display_store_word(b));
  printf("%s", display_store_word(result));
#endif

  // Find smaller number and shift it so the exponents are the same
  return(result);
}

////////////////////////////////////////////////////////////////////////////////
//
// FP Divide
//
////////////////////////////////////////////////////////////////////////////////

// result = a / b

SINGLE_WORD fp_divide(ESC_STATE *s, SINGLE_WORD a, SINGLE_WORD b)
{
  int exp_a, exp_b, exp_r;
  int exp_diff;
  int digits_a, digits_b, digits_r;
  int sign_a, sign_b, sign_r;
  SINGLE_WORD result;
  SINGLE_WORD shifted_digits;   // arg a shifted
  SINGLE_WORD tested_digits;    // arg b test against and subtracted from
  SINGLE_WORD added_digits;         // number added to result

  // Before we do any calculations, move the MS digit to the left most position so we get
  // full resolution for the result. This is done to both a and b

#if DEBUG_FP
  printf("\n%s", __FUNCTION__);
  printf("\na:%016X b:%016X", a, b);
#endif

  a = sw_msd_to_left(a);
  b = sw_msd_to_left(b);

  digits_a  =  STORE_GET_DIGITS(a);
  digits_b  =  STORE_GET_DIGITS(b);
  sign_a =  STORE_GET_SIGN(a);
  sign_b =  STORE_GET_SIGN(b);
  exp_a = STORE_GET_EXPONENT(a);
  exp_b = STORE_GET_EXPONENT(b);

#if DEBUG_FP
  printf("\nAfter MSD shift");
  printf("\na:%016X b:%016X", a, b);
  printf("\ndigits_r       = %016X", digits_r);
#endif
  
  // The number added is a 1, but is in various digit positions
  // Sign added just before addition
  added_digits = 1;

  // Always shift arg b
  shifted_digits = digits_b;

  // Always test against arg a
  tested_digits = digits_a;

  // result digits, sign and exponent added later
  digits_r = 0;
  digits_r = STORE_SET_SIGN(digits_r, WORD_SIGN_PLUS);

  // Work without sign or exponent
  shifted_digits = STORE_SET_SIGN(shifted_digits, WORD_SIGN_PLUS);
  tested_digits  = STORE_SET_SIGN(tested_digits,  WORD_SIGN_PLUS);
  
#if DEBUG_FP
  printf("\n%s: ", __FUNCTION__);
  printf("\na:%016X  b:%016X", a, b); 
  printf("\nadded_digits   = %016X", added_digits);
  printf("\ntested_digits  = %016X", tested_digits);
  printf("\nshifted_digits = %016X", shifted_digits);
#endif


  // We shift until a non zero digit is in RH side of shifted digits
  int number_of_shifts = 0;

  if( (shifted_digits & 0x00FFFFFF)  == 0 )
    {
      // Divide by zero
#if DEBUG_FP_SUMMARY
      printf("\n%s: %s / ", __FUNCTION__, display_store_word(a));
      printf("%s = "      , display_store_word(b));
      printf("%s"         , display_store_word(result));
      
      printf("\nDivide by zero");
#endif
      // Error
      return(0xC0999999);
    }

#if 1
  while( (shifted_digits & 0x00F00000) == 0 )
    {
      shifted_digits <<=4;
      added_digits <<= 4;
      number_of_shifts++;
    }
#endif
  
  // We add one arg <digit> number of times then shift until all 6 digits are
  // processed.
  // Exponent then sorted out (added)
  // Sign then sorted out (xor'd)
  // Any overflow with addition => error

  shifted_digits = STORE_SET_SIGN(shifted_digits, WORD_SIGN_PLUS);
	
#if DEBUG_FP
  printf("\n**After initial shift left**");
  printf("\ndigits_r       = %016X", digits_r);
  printf("\nadded_digits   = %016X", added_digits);
  printf("\ntested_digits  = %016X", tested_digits);
  printf("\nshifted_digits = %016X", shifted_digits);
#endif
  
  int out = 100;
  added_digits = 0xC0100000;
  
  for(int i=0; (i<6) && (out > 0); i++,out--)
    {
      // Can we subtract?
#if DEBUG_FP
      printf("\n**Sub possible?**");
      printf("\ndigits_r       = %016X", digits_r);
      printf("\nadded_digits   = %016X", added_digits);
      printf("\ntested_digits  = %016X", tested_digits);
      printf("\nshifted_digits = %016X", shifted_digits);
#endif
      
      while( (REMOVED_SW_SIGN(tested_digits) >= REMOVED_SW_SIGN(shifted_digits)) && (REMOVED_SW_SIGN(shifted_digits) != 0) )
	{
#if DEBUG_FP
	  printf("\n**Can subtract**");
#endif
	  
	  // Add one to digit position
	  digits_r = fp_add(s, digits_r, added_digits, 0);
	  
	  tested_digits = fp_subtract(s, tested_digits, shifted_digits, 0);
#if DEBUG_FP
	  printf("\n**In Loop**");
	  printf("\ndigits_r       = %016X", digits_r);
	  printf("\nadded_digits   = %016X", added_digits);
	  printf("\ntested_digits  = %016X", tested_digits);
	  printf("\nshifted_digits = %016X", shifted_digits);
#endif
	}
      
      // Move to next position
      // Remove sign
      shifted_digits = REMOVED_SW_SIGN(shifted_digits);
      added_digits  = REMOVED_SW_SIGN(added_digits);
      
      // Shift
      added_digits   >>= 4;
      shifted_digits >>= 4;
      shifted_digits = STORE_SET_SIGN(shifted_digits, WORD_SIGN_PLUS);
      added_digits   = STORE_SET_SIGN(added_digits,  WORD_SIGN_PLUS);
    }
  
#if DEBUG_FP
  printf("\n**out of loops**");
  printf("\ndigits_r       = %016X", digits_r);
  printf("\nadded_digits   = %016X", added_digits);
  printf("\ntested_digits  = %016X", tested_digits);
  printf("\nshifted_digits = %016X", shifted_digits);
#endif
  
  
#if DEBUG_FP
  printf("\nexp_a :%016X  exp_b :%016X", exp_a, exp_b);
  printf("\nsign_a:%016X  sign_b:%016X", sign_a, sign_b);
  printf("\ndigits_a:%016X  digits_b:%016X digits_r:%016X", digits_a, digits_b, digits_r); 
#endif

  result = digits_r;

  //exp_r = exp_a - exp_b + 5 - number_of_shifts;
  exp_r = 5 - (exp_b - exp_a); // + 5 - number_of_shifts;
  result = STORE_SET_EXPONENT(result, exp_r);
    
#if DEBUG_FP
  printf("\nexp_r :%016X", exp_r);
#endif

  while( exp_r > 6 )
    {
      printf("\nsw loop");
#if DEBUG_FP
      printf("\nresult:%016X", result); 
#endif

      // Shift result right so it fits
      result = sw_shift_right(result, 1);
      exp_r--;
    }

#if DEBUG_FP
  printf("\nexp_r after normalise:%016X", exp_r);
#endif
  
  // Put exponent back as same number of decimal places as arg b
  result = STORE_SET_EXPONENT(result, exp_r);

  // Put sign back
  if( sign_a == sign_b )
    {
      sign_r = WORD_SIGN_PLUS;
    }
  else
    {
      sign_r = WORD_SIGN_MINUS;
    }

  result = STORE_SET_SIGN(result, sign_r);
  
#if DEBUG_FP
  printf("\na:%s", display_store_word(a));
  printf("\nb:%s", display_store_word(b));
  printf("\nNum of shifts:%d", number_of_shifts);
  printf("\nresult:%s", display_store_word(result));
  
#endif

#if DEBUG_FP_SUMMARY
  printf("\n%s: %s / ", __FUNCTION__, display_store_word(a));
  printf("%s = "      , display_store_word(b));
  printf("%s"         , display_store_word(result));
#endif

  // Find smaller number and shift it so the exponents are the same
  return(result);
}

////////////////////////////////////////////////////////////////////////////////
//
// IAR handling
//
// IAR is a simple two digit counter, plus a top half/bottom half flag for
// 4 digit instructions
//
// Logic:
//   If in KI reset then IAR does not advance
//
//   Digit a determines type of instruction
//    If a = 7,8, or 9 then IAR incremented and half flag cleared (it shouldn't be set)
//    Otherwise
//       If half flag is set then clear it and increment IAR
//       Otherwise set half flag
//
// Note: IAR is BCD
//
////////////////////////////////////////////////////////////////////////////////
//

// Load IAR
// Only lower two digits are loaded so if we are in extracode we stay in extracode
//
//
// We can detect exiting an extracode here if the hundreds digit goes from 1 (or non-zero?)
// to zero

void load_iar_bcd(ESC_STATE *s, int bcdval)
{
#if DEBUG_LOAD_IAR
  printf("\n%s:%08X", __FUNCTION__, bcdval);
#endif
  
  // Exiting extracode?
  if( IS_EXTRACODE )
    {
#if DEBUG_EXTRACODE
      printf("\n*** IAR being loaded in extracode***");
#endif
      if( (bcdval & 0xF00) == 0 )
        {
#if DEBUG_EXTRACODE
          printf("\n*** IAR will be in lower store ***");
#endif
          s->exiting_extracode = 1;

#if DEBUG_EXTRACODE
          printf("\nexiting_extracode=%d\n", s->exiting_extracode);
#endif
          
          // We will be exiting extracode, put up the appropriate display for
          // stage C, if we are in extracode step setting
          if( setup_step_extracode )
            {
#if DEBUG_EXTRACODE
              printf("\n*** Exiting extracode ***");
#endif
              s->stop = 1;
              
              // Put display up
              display_line_2(s, DISPLAY_UPDATE);
              display_on_line(s, DISPLAY_UPDATE, 2, "%3X    %s", s->Aa1, display_store_word(load_from_store(s, s->Aa1)));
              display_on_line(s, DISPLAY_UPDATE, 3, "%3X    %s", s->Aa2, display_store_word(load_from_store(s, s->Aa2)));
              display_on_line(s, DISPLAY_UPDATE, 4, "%3X    %s", s->Aa3, display_store_word(load_from_store(s, s->Aa3)));
              display_on_line(s, DISPLAY_UPDATE, 5, "               ");
            }
          else
            {
              // Not stepping extracode, so we would have been in run mode.
              // We need to stop if not running
              //s->run = 0;
              s->extracode_run = 0;
              if( !s->run )
                {
                  s->stop = 1;
                }
            }
        }
      else
        {
          // Not exiting an extracode subroutine
          s->exiting_extracode = 0;

#if DEBUG_EXTRACODE
          printf("\nexiting_extracode=%d\n", s->exiting_extracode);
#endif
        }
    }
  
  // Clear current digits
  //  s->iar.address &= 0x000;
  s->iar.address = BOUND_ADDRESS(bcdval);

#if DEBUG_LOAD_IAR
  printf("\n%s:%08X", __FUNCTION__, s->iar.address);
#endif

}

////////////////////////////////////////////////////////////////////////////////
//
// Calculate the address to put in the LINK register
//
// This is the next address, ignoring half addresses
//
////////////////////////////////////////////////////////////////////////////////

IAR calculate_link_address(IAR current_iar)
{
  IAR retval = current_iar;

  // We return the address of the next word

  // IAR is BCD so add one

  // Wrap from 099 to 000
  if( retval.address == 0x99 )
    {
      retval.address = 0x000;
    }
  else
    {
      retval.address = single_sum_normalise(bcd_addition_single(retval.address,1));
    }

  // Bound to three digits
  retval.address &= 0xFFF;
  retval.a_flag = 0;

  return(retval);
}


//------------------------------------------------------------------------------
//
// Move to next IAR while executing code.
//
// Also detects instrcution as single address instructions and three address
// instructions are treated differently
//

void next_iar(ESC_STATE *s)
{
  FN_ENTRY;

#if DEBUG_NEXT_IAR
  printf("\nIAR before:%s", display_iar(s, SPEC_IAR));
#endif

  int digit_a = INST_A_FIELD(s->instruction_register);
  
  if( s->ki_reset_flag && !IS_EXTRACODE )
    {
      return;
    }
  
  switch(digit_a)
    {
    case 7:
    case 8:
    case 9:
      if( s->iar.a_flag )
	{
	  warning_msg("8 digit instruction has A flag set");
	}
      
      // 8 digit instruction so move to next address
      // While executing, address wraps from 0x99 to 0x00
      if( s->iar.address == 0x99 )
        {
          s->iar.address = 0x000;
        }
      else
        {
          load_iar_bcd(s, single_sum_normalise(bcd_addition_single(s->iar.address,1)));
        }

      // IAR only three digits
      s->iar.address &= 0xFFF;
      s->iar.a_flag = 0;
      break;
      
    case 0:
    case 1:
    case 2:
    case 3:
    case 4:
    case 5:
    case 6:
      if( s->iar.a_flag )
	{
          // While executing, address wraps from 0x99 to 0x00
          if( s->iar.address == 0x99 )
            {
              s->iar.address = 0x000;
            }
          else
            {
              load_iar_bcd(s, single_sum_normalise(bcd_addition_single(s->iar.address,1)));
            }
          
	  // IAR only three digits
	  s->iar.address &= 0xFFF;
	  s->iar.a_flag = 0;
	}
      else
	{
	  s->iar.a_flag = !(s->iar.a_flag);
	}
      break;
      
    default:
      // error
      error_msg("Unknown digit a");
      
      break;
    }

#if DEBUG_NEXT_IAR
  printf("\nIAR after: %s", display_iar(s, SPEC_IAR));
#endif
  
  FN_EXIT;
}

////////////////////////////////////////////////////////////////////////////////
//
//  Enter ERROR state
// 
////////////////////////////////////////////////////////////////////////////////

void enter_error_state(ESC_STATE *s, char *msg)
{
  // Stop execution
  s->run  = 0;
  s->stop = 1;

  display_on_line(s, DISPLAY_UPDATE, 2, "            %c  ", ERROR_RECTANGLE);

  printf("\n**** Error state:%s ****\n", msg);
  printf("\n    IAR:%s\n", display_iar(s, SPEC_IAR));
}


////////////////////////////////////////////////////////////////////////////////
//
// Displays standard line 2 with IAR and instruction
//
// Instruction display matches Fig 10 in IEE document.
//
// Three address instructions displayed fully.
// Instructions at XX displaye don left of field
// Instructions at XXA displaye don right
//
////////////////////////////////////////////////////////////////////////////////

void display_line_2(ESC_STATE *s, int display)
{
  char inst_str[9];
  int digit_a;
  
  inst_str[8] = '\0';
  
  if( !display )
    {
      return;
    }
  
  // We display IAR and the decoded digits of the instruction from the stage A decode

  // A different display if we have just exited an extracode or we are in an extracode subroutine 
  // AUX IAR is used to find the instruction, as that works for the extracodes.
  // the previous stages are from the extracode subroutine instructions for extracodes.
  SINGLE_WORD extracode_inst = load_from_store(s, s->aux_iar.address);

#if DEBUG_EXTRACODE
  printf("\nexiting extracode = %d extracode_inst=%08X", s->exiting_extracode, extracode_inst);
#endif
  
  // If stepping extracode then we want to see the subroutine instructions

  digit_a = s->inst_digit_a;
  
  if( s->exiting_extracode || (IS_EXTRACODE && !setup_step_extracode) )
    {
      // Force inst_digit_a to use the extracode instruction digit a, not the last subroutine
      // instruction digit a
      digit_a = INST_A_FIELD(extracode_inst);

#if DEBUG_EXTRACODE
      printf("\nUsing digit A set to %d", digit_a);
#endif
    }
  
  switch(digit_a)
    {
    case 7:
    case 8:
    case 9:
      if( s->exiting_extracode || (IS_EXTRACODE && !setup_step_extracode) )
        {
          // Get the instruction from the auxiliary IAR as that has the extracode address in it
          // The auxiliary IAR isn't updated during th eextracode subroutine execution

          
          inst_str[0] = INST_A_FIELD(extracode_inst)+'0';
          inst_str[1] = INST_B_FIELD(extracode_inst)+'0';
          inst_str[2] = INST_C_FIELD(extracode_inst)+'0';
          inst_str[3] = INST_D_FIELD(extracode_inst)+'0';
          inst_str[4] = INST_E_FIELD(extracode_inst)+'0';
          inst_str[5] = INST_F_FIELD(extracode_inst)+'0';
          inst_str[6] = INST_G_FIELD(extracode_inst)+'0';
          inst_str[7] = INST_H_FIELD(extracode_inst)+'0';
        }
      else
        {
          inst_str[0] = INST_A_FIELD(s->instruction_register)+'0';
          inst_str[1] = INST_B_FIELD(s->instruction_register)+'0';
          inst_str[2] = INST_C_FIELD(s->instruction_register)+'0';
          inst_str[3] = INST_D_FIELD(s->instruction_register)+'0';
          inst_str[4] = INST_E_FIELD(s->instruction_register)+'0';
          inst_str[5] = INST_F_FIELD(s->instruction_register)+'0';
          inst_str[6] = INST_G_FIELD(s->instruction_register)+'0';
          inst_str[7] = INST_H_FIELD(s->instruction_register)+'0';
        }
      break;

    default:
      if( s->aux_iar.a_flag )
	{
	  inst_str[0] = ' ';
	  inst_str[1] = ' ';
	  inst_str[2] = ' ';
	  inst_str[3] = ' ';
	  inst_str[4] = INST_E_FIELD(s->instruction_register)+'0';
	  inst_str[5] = INST_F_FIELD(s->instruction_register)+'0';
	  inst_str[6] = INST_G_FIELD(s->instruction_register)+'0';
	  inst_str[7] = INST_H_FIELD(s->instruction_register)+'0';
	}
      else
	{
	  inst_str[0] = INST_A_FIELD(s->instruction_register)+'0';
	  inst_str[1] = INST_B_FIELD(s->instruction_register)+'0';
	  inst_str[2] = INST_C_FIELD(s->instruction_register)+'0';
	  inst_str[3] = INST_D_FIELD(s->instruction_register)+'0';
	  inst_str[4] = ' ';
	  inst_str[5] = ' ';
	  inst_str[6] = ' ';
	  inst_str[7] = ' ';
	}
      break;
    }

#if DEBUG_STOP
  char stopch;
  stopch = (s->stop)?'S':' ';
#else
  char stopch = ' ';
#endif
  
  if( s->ki_reset_flag )
    {
      // Keyboard inout on line 1?  **TODO**
      display_on_line(s, DISPLAY_UPDATE, 2, "K  %s %c %c", inst_str, s->stage, stopch);
    }
  else
    {

      // If we are exiting extracode then we want to display the AUX IAR (extracode instruction
      // store address). Unless we are stepping extracode then we want to display the
      // subroutine instruction address
      if( s->exiting_extracode || (IS_EXTRACODE && !setup_step_extracode))
        {
          // In an extracode instruction, if we aren't stepping through the extracode
          // then the IAR is not showing the program address, but the extracode
          // instruction address. Do not display it.
          //          display_on_line(s, DISPLAY_UPDATE, 1, "%02s",       display_iar(s, SPEC_IAR));
          //display_on_line(s, DISPLAY_UPDATE, 1, "   ");
          display_on_line(s, DISPLAY_UPDATE, 2, "%02s %s %c %c", display_iar(s, SPEC_AUX_IAR), inst_str, s->stage, stopch);
        }
      else
        {
          //     display_on_line(s, DISPLAY_UPDATE, 1, "%02s",       display_iar(s, SPEC_IAR));
          display_on_line(s, DISPLAY_UPDATE, 2, "%02s %s %c %c", display_iar(s, SPEC_IAR), inst_str, s->stage, stopch);
        }

    }
}

////////////////////////////////////////////////////////////////////////////////


void display_three_address_values(ESC_STATE *s, int display)
{
  printf("\n%s display=%d", __FUNCTION__, display);

  if( display )
    {
      // If exiting from an extracode subroutine, display the extracode values, not
      // the s->Aa values as they will be from the last subroutine instruction.
      if( s->exiting_extracode )
        {
          display_on_line(s, display, 3, "%s", display_store_and_contents_from_tar(s, 0x100));
          display_on_line(s, display, 4, "%s", display_store_and_contents_from_tar(s, 0x101));
          display_on_line(s, display, 5, "%s", display_store_and_contents_from_tar(s, 0x102));
        }
      else
        {
          display_on_line(s, display, 3, "%s", display_store_and_contents(s, s->Aa1));
          display_on_line(s, display, 4, "%s", display_store_and_contents(s, s->Aa2));
          display_on_line(s, display, 5, "%s", display_store_and_contents(s, s->Aa3));
        }
    }
}

////////////////////////////////////////////////////////////////////////////////
//
// Instruction decode
//
// Completes instructions that require a third stage
// Moves IAR to next instruction

void stage_c_decode(ESC_STATE *s, int display)
{
  SINGLE_WORD a1v, a2v, a3v;
  SINGLE_WORD tst;
  int extreme_left_digit = 0;
  int extreme_right_digit = 0;
  int src_sign;
  int is_gt_zero = 0;
  int is_zero = 0;
  int is_lt_zero = 0;
  REGISTER_SINGLE_WORD  store_value;
  
  FN_ENTRY_DISPLAY;
  
#if DEBUG_STAGES
  printf(" [Stage C: AUXIAR:%03X%s IAR:%03X%s] (top entry)", s->aux_iar.address, s->aux_iar.a_flag?"A":" ", s->iar.address, s->iar.a_flag?"A":" ");
#endif

  // The input instructions stop at stage B so that the keyboard register can be loaded with
  // a value. At the beginning of stage C, the entered value is loaded as required.
  
  if( s->on_restart_load_aa )
    {
#if DEBUG_RESTART
      printf("\nLoading aa (%02X) with %s", s->inst_aa, display_store_word(s->keyboard_register));
#endif
      // Load aa with KB register
      write_sw_to_store(s, s->inst_aa, s->keyboard_register);
      s->on_restart_load_aa = 0;
      s->stop = 0;
      
      clear_keyboard_register(s);
    }
  
  if( s->on_restart_load_aa1 )
    {
#if DEBUG_RESTART
      printf("\nLoading Aa1 (%02X) with %s", s->Aa1, display_store_word(s->keyboard_register));
#endif
      // Load Aa1 with KB register
      write_sw_to_store(s, s->Aa1, s->keyboard_register);
      s->on_restart_load_aa1 = 0;
      s->stop = 0;
      clear_keyboard_register(s);
    }
  
  // Decode the instruction
  // First the digits 1-4
  // A different display if we have just exited an extracode. 
  // AUX IAR is used to find the instruction, as that works for the extracodes.
  // the previous stages are from the extracode subroutine instructions for extracodes.
  
  SINGLE_WORD extracode_inst = load_from_store(s, s->aux_iar.address);

#if DEBUG_EXTRACODE
  printf("\nexiting extracode = %d extracode_inst=%08X", s->exiting_extracode, extracode_inst);
#endif
  
  // If we are stepping extracode then we do want to display the subroutine instruction
#if 0
  if( s->exiting_extracode || (IS_EXTRACODE && !setup_step_extracode) )
    {
      // Force inst_digit_a to use the extracode instruction digit a, not the last subroutine
      // instruction digit a
      // Do same for digit b
      // This ensures the correct instruction is decoded if exiting extracode
      s->inst_digit_a = INST_A_FIELD(extracode_inst);
      s->inst_digit_b = INST_B_FIELD(extracode_inst);
    }
#endif
  
#if DEBUG_EXTRACODE
      printf("\nInst digit A set to %d", s->inst_digit_a);
#endif

#if DEBUG_STAGES
  printf(" [Stage C: AUXIAR:%03X%s IAR:%03X%s] (entry)", s->aux_iar.address, s->aux_iar.a_flag?"A":" ", s->iar.address, s->iar.a_flag?"A":" ");
#endif

  switch(s->inst_digit_a)
    {
    case 0:
      switch(s->inst_digit_b)
	{
	case 0:
          register_assign_sum_register_literal(s, s->reginst_rc, s->reginst_rc, s->reginst_literal);
          break;

        case 1:
	  // (Rc) <= (Rc) - d
	  register_assign_sub_register_literal(s, s->reginst_rc, s->reginst_rc, s->reginst_literal);
	  break;

	case 2:
	  // (Rc) <= d - (Rc)
	  register_assign_sub_literal_register(s, s->reginst_rc, s->reginst_literal, s->reginst_rc);

	  // display_line_2(s, display);
	  // display_on_line(s, display, 3, "%s", display_register_and_contents(s, s->reginst_rc));
	  // display_on_line(s, display, 4, "               ");
	  // display_on_line(s, display, 5, "               ");
	  // display_on_line(s, display, 6, "               ");
	  break;
	  
	case 3:
	  // (Rc) <= d
	  register_assign_register_literal(s, s->reginst_rc, s->reginst_literal);

	  // display_line_2(s, display);
	  // display_on_line(s, display, 3, "%s", display_register_and_contents(s, s->reginst_rc));
	  // display_on_line(s, display, 4, "               ");
	  // display_on_line(s, display, 5, "               ");
	  // display_on_line(s, display, 6, "               ");
	  break;

	case 4:
	  // Not used
	  break;
	  
	case 5:
	  // Test (Rc)
#if DEBUG_TEST
	  printf("\nTEST (5) [R%d] = %08X", s->reginst_rc, read_any_size_register_absolute(s, s->reginst_rc));
#endif
	  switch(s->inst_digit_d)
	    {
	    case 0:
	      is_zero = 0;
	      
#if DEBUG_TEST
	      printf("\nTEST (5) ");
#endif
	      
	      if( IS_SW_REGISTER(s->reginst_rc) )
		{
                  //		  if( (SW_REG_CONTENTS(s->reginst_rc) & 0xFFFFFF) == 0 )
                  if( (read_register(s, s->reginst_rc) & 0xFFFFFF) == 0 )
		    {
		      is_zero = 1;
		    }
		}

	      if( IS_DW_REGISTER(s->reginst_rc) )
		{
		  if( (read_register(s, s->reginst_rc) & 0xFFFFFFFFFFFF) == 0 )
		    {
		      is_zero = 1;
		    }
		}
	      
	      if( is_zero )
		{
#if DEBUG_TEST
		  printf("\nCL = 1 after test (is = 0)");
#endif
		  s->control_latch = 1;
		}
	      else
		{
#if DEBUG_TEST
		  printf("\nCL = 0 after test (is not = 0)");
#endif
		  s->control_latch = 0;
		}
	      break;
	      
	    case 1:
	      is_gt_zero = 0;
	      
	      if( IS_SW_REGISTER(s->reginst_rc) )
		{
#if DEBUG_TEST
		  printf("\nR%d = %016X", s->reginst_rc, read_register(s, s->reginst_rc));
                  printf("\nR%d = %08X", s->reginst_rc, read_register(s, s->reginst_rc));
                  printf("\nR%d = %08X", s->reginst_rc, SW_SIGN(read_register(s, s->reginst_rc)));
#endif

                  //		  if( (SW_SIGN(SW_REG_CONTENTS(s->reginst_rc)) == WORD_SIGN_PLUS) && ((SW_REG_CONTENTS(s->reginst_rc) & 0xFFFFFF) != 0) )
                  if( (SW_SIGN(read_register(s, s->reginst_rc)) == WORD_SIGN_PLUS) &&
                      ((read_register(s, s->reginst_rc) & 0xFFFFFF) != 0) )
		    {
		      is_gt_zero = 1;
		    }
		}

	      if( IS_DW_REGISTER(s->reginst_rc) )
		{
		  if( (DW_SIGN(read_register(s, s->reginst_rc)) == WORD_SIGN_PLUS) && ((read_register(s, s->reginst_rc) & 0xFFFFFFFFFFFF) != 0) )
		    {
		      is_gt_zero = 1;
		    }
		}
	      
	      if( is_gt_zero )
		{
#if DEBUG_TEST
		  printf("\nCL = 1 after test (is > 0)");
#endif
		  s->control_latch = 1;
		}
	      else
		{
#if DEBUG_TEST
		  printf("\nCL = 0 after test (is not > 0)");
#endif
		  s->control_latch = 0;
		}
	      break;
	      
	    case 2:
              // Check for R < 0
              // If zero then no
              // The reason for the check of zero is that it is possible for the sign to be -ve
              // and the value to be zero.
	      is_lt_zero = 0;
              is_zero = 0;
	      
#if DEBUG_TEST
	      printf("\nTEST (5) ");
#endif
              
	      if( IS_SW_REGISTER(s->reginst_rc) )
		{
		  if( (read_register(s, s->reginst_rc) & 0xFFFFFF) == 0 )
		    {
		      is_zero = 1;
		    }
		}

	      if( IS_DW_REGISTER(s->reginst_rc) )
		{
		  if( (read_register(s, s->reginst_rc) & 0xFFFFFFFFFFFF) == 0 )
		    {
		      is_zero = 1;
		    }
		}
	      
	      if( is_zero )
		{
#if DEBUG_TEST
		  printf("\nCL = 0 after test (is < 0) as is 0");
#endif
		  s->control_latch = 0;
		}
              else
                {
#if DEBUG_TEST
		  printf("\nNot zero, test sign...");
#endif

                  // Not zero, so check sign
                  is_lt_zero = 0;
                  
                  if( IS_SW_REGISTER(s->reginst_rc) )
                    {
                      if( SW_SIGN(read_register(s, s->reginst_rc)) == WORD_SIGN_MINUS )
                        {
#if DEBUG_TEST
                          printf("\nSW value < 0 (%016X)", read_register(s, s->reginst_rc));
#endif

                          is_lt_zero = 1;
                        }
                    }
                  
                  if( IS_DW_REGISTER(s->reginst_rc) )
                    {
                      if( DW_SIGN(read_register(s, s->reginst_rc)) == WORD_SIGN_MINUS )
                        {
                          is_lt_zero = 1;
                        }
                    }
                }
              
	      if( is_lt_zero )
		{
#if DEBUG_TEST
		  printf("\nCL = 1 after test");
#endif
		  s->control_latch = 1;
		}
	      else
		{
#if DEBUG_TEST
		  printf("\nCL = 0 after test");
#endif
		  s->control_latch = 0;
		}

	      break;
	      
	    case 3:

	      if( IS_SW_REGISTER(s->reginst_rc) )
		{
		  extreme_left_digit = (read_register(s, s->reginst_rc) & 0x00F00000) >> (5*4);
		}

	      if( IS_DW_REGISTER(s->reginst_rc) )
		{
		  extreme_left_digit = (read_register(s, s->reginst_rc) & 0x0000F00000000000) >> (11*4);
		}

#if DEBUG_TEST
	      printf("\nTEST extreme left:%d ", extreme_left_digit);
#endif
	      
	      if( extreme_left_digit == 0 )
		{
		  s->control_latch = 1;
		}
	      else
		{
		  s->control_latch = 0;
		}
	      break;


	    case 4:
	      if( IS_SW_REGISTER(s->reginst_rc) )
		{
		  extreme_right_digit = (read_register(s, s->reginst_rc) & 0x0000000F) >> 0;
		}
	      
	      if( IS_DW_REGISTER(s->reginst_rc) )
		{
		  extreme_right_digit = (read_register(s, s->reginst_rc) & 0x000000000000000F) >> 0;
		}
	      
#if DEBUG_TEST
	      printf("\nTEST extreme right:%d ", extreme_right_digit);
#endif
	      
	      if( extreme_right_digit == 0 )
		{
		  s->control_latch = 1;
		}
	      else
		{
		  s->control_latch = 0;
		}
	      break;
	      
	    }

	  // display_line_2(s, display);
	  // clear_lines_3_to_6(s, display);
	  // display_any_size_register_on_line(s, display, 3, s->reginst_rc,  CONTENTS);
	  // display_on_line(s, display, 6, "CL            %d", s->control_latch);
	  
	  break;
	  
	  // Shift (Rc) left d places 
	case 6:
	  register_left_shift(s, s->reginst_rc, s->reginst_literal);

	  // display_line_2(s, display);
	  // clear_lines_3_to_6(s, display);
	  // display_two_any_size_register_on_line(s, display, 3, s->reginst_rc, s->reginst_rd, CONTENTS);
	  break;
	  
	  // Shift (Rc) right d places
	case 7:
	  register_right_shift(s, s->reginst_rc, s->reginst_literal);

	  // display_line_2(s, display);
	  // clear_lines_3_to_6(s, display);
	  // display_two_any_size_register_on_line(s, display, 3, s->reginst_rc, s->reginst_rd, CONTENTS);
	  break;

	case 8:
	  // Not used
          enter_error_state(s, "08xx not used");
	  break;

	case 9:
	  // Not used
          enter_error_state(s, "09xx not used");
	  break;
        }

      // All instructions move to next IAR (no branches)
      next_iar(s);
      break;
      
    case 1:
#if DEBUG_STAGES
      printf("\ninst_digit_b:%d", s->inst_digit_b);
#endif
      switch(s->inst_digit_b)
	{
	case 0:
	  // Add registers
	  register_assign_sum_register_register(s, s->reginst_rc, s->reginst_rc, s->reginst_rd);
	  // display_line_2(s, display);
	  // display_two_any_size_register_on_line(s, display, 3, s->reginst_rc, s->reginst_rd, CONTENTS);
	  break;

	case 1:
	  // Subtract registers (Rc)-(Rd)
	  register_assign_sub_register_register(s, s->reginst_rc, s->reginst_rc, s->reginst_rd);
	  // display_line_2(s, display);
	  // display_two_any_size_register_on_line(s, display, 3, s->reginst_rc, s->reginst_rd, CONTENTS);
	  break;
	  
	case 2:
	  // Subtract registers (Rd)-(Rc)
#if DEBUG_STAGES
          printf("\nSubtract registers (Rd)-(Rc)");
#endif

	  register_assign_sub_register_register(s, s->reginst_rc, s->reginst_rd, s->reginst_rc);
	  // display_line_2(s, display);
	  // display_two_any_size_register_on_line(s, display, 3, s->reginst_rc, s->reginst_rd, CONTENTS);
	  break;
	  
	case 3:
	  // Register assign (Rc) <-(Rd)
	  register_assign_register(s, s->reginst_rc, s->reginst_rd);
	  // display_line_2(s, display);
	  // display_two_any_size_register_on_line(s, display, 3, s->reginst_rc, s->reginst_rd, CONTENTS);
	  break;

	  // Copy right hand 6 digits of Rd into Rc. Works with single and double length registers
	case 4:
	  // First the sign
	  src_sign = any_size_sign(s, s->reginst_rd);
	  //@printf("\nsrc_sign=%d", src_sign);
	  
	  set_any_size_sign(s, s->reginst_rc, src_sign);

	  //printf("\nR[]=%08X", s->R[s->reginst_rc]);
	  
	  // Then the RH six digits
	  int rh6 = any_size_rh6(s, s->reginst_rd);
	  set_any_size_rh6(s, s->reginst_rc, rh6);
	  //printf("\nR[]=%08X", s->R[s->reginst_rc]);

	  // display_line_2(s, display);
	  // display_two_any_size_register_on_line(s, display, 3, s->reginst_rc, s->reginst_rd, CONTENTS);
	  break;

	case 5:
	  // Not used
	  break;
	  
	  // Shift (Rc) left (Rd) places 
	case 6:
	  register_left_shift(s, s->reginst_rc, read_any_size_register_absolute(s, s->reginst_rd));

	  // display_line_2(s, display);
	  // display_two_any_size_register_on_line(s, display, 3, s->reginst_rc, s->reginst_rd, CONTENTS);
	  break;
	  
	  // Shift (Rc) right (Rd) places
	case 7:
	  register_right_shift(s, s->reginst_rc, read_any_size_register_absolute(s, s->reginst_rd));

	  // display_line_2(s, display);
	  // display_two_any_size_register_on_line(s, display, 3, s->reginst_rc, s->reginst_rd, CONTENTS);
	  break;

	case 8:
	  // Not used
          enter_error_state(s, "18xx not used");
	  break;

	case 9:
          // This instruction is used to stop and display X,Y,Z when running in an extracode subroutine.
          // Check if we are in an extracode and behave appropriately.

          if( IS_EXTRACODE )
            {
              //
              // Stop and display X, Y, Z
              // 
              s->stop = 1;
              s->inst_update_display = 1;
              // display_line_2(s, DISPLAY_UPDATE);
              // display_on_line(s, DISPLAY_UPDATE, 3, "%3X    %s", s->Aa1, display_store_word(load_from_store(s, s->Aa1)));
              // display_on_line(s, DISPLAY_UPDATE, 4, "%3X    %s", s->Aa2, display_store_word(load_from_store(s, s->Aa2)));
              // display_on_line(s, DISPLAY_UPDATE, 5, "%3X    %s", s->Aa3, display_store_word(load_from_store(s, s->Aa3)));
              // display_on_line(s, DISPLAY_UPDATE, 6, "               ");

            }
          else
            {
              // Stop and display (Rc) and (Rd)
              // 
              s->stop = 1;
              s->inst_update_display = 1;
              // display_line_2(s, DISPLAY_UPDATE);
              // display_two_any_size_register_on_line(s, DISPLAY_UPDATE, 3, s->reginst_rc, s->reginst_rd, CONTENTS);
            }
	  break;
	}
      
      // Instruction complete, move IAR on
      next_iar(s);

      break;

    case 2:
    case 3:
    case 4:
    case 5:
    case 6:
      switch(s->inst_digit_b)
	{
	case 0:
          // Copy (Aa) into R0 and R1 as follows. If Aa contains
	  // data (recognisable by a sign in digit position 1), copy the
	  // exponent digit into R0 and the sign and significant digits into
	  // R1. If Aa contains an instruction (recognisable by a decimal
	  // digit in position 1), copy the left-hand four digits into Ro and
	  // the right-hand four digits into Ri
          
	  // Fixed registers
	  s->reginst_rc = 0;
	  s->reginst_rd = 1;
	  
	  store_value = load_from_store(s, s->inst_aa);
	  
	  if( (STORE_GET_SIGN(store_value)==WORD_SIGN_PLUS) || (STORE_GET_SIGN(store_value)==WORD_SIGN_MINUS) )
	    {
	      // Data (value)
#if 0
	      s->R[0] = STORE_GET_EXPONENT(store_value);
	      s->R[0] = SET_SW_SIGN(s->R[0], WORD_SIGN_PLUS);
	      s->R[1] = STORE_GET_DIGITS(store_value);
	      s->R[1] = SET_SW_SIGN(s->R[1], STORE_GET_SIGN(store_value));
#endif
	      write_register(s, 0, STORE_GET_EXPONENT(store_value));
	      write_register(s, 0, SET_SW_SIGN(read_register(s, 0), WORD_SIGN_PLUS));
              write_register(s, 1, STORE_GET_DIGITS(store_value));
              write_register(s, 1, SET_SW_SIGN(read_register(s, 1), STORE_GET_SIGN(store_value)));

	    }
	  else
	    {
	      // Instruction
#if 0
	      s->R[0] = STORE_GET_LH4_DIGITS(store_value);
	      s->R[0] = SET_SW_SIGN(s->R[0], WORD_SIGN_PLUS);
	      s->R[1] = STORE_GET_RH4_DIGITS(store_value);
	      s->R[1] = SET_SW_SIGN(s->R[1], WORD_SIGN_PLUS);
#endif
	      write_register(s, 0, STORE_GET_LH4_DIGITS(store_value));
	      write_register(s, 0, SET_SW_SIGN(read_register(s, 0), WORD_SIGN_PLUS));
	      write_register(s, 1, STORE_GET_RH4_DIGITS(store_value));
	      write_register(s, 1, SET_SW_SIGN(read_register(s, 1), WORD_SIGN_PLUS));

	    }

	  next_iar(s);
	  
	  // display_line_2(s, display);
	  // display_on_line(s, display, 3, "               ");
	  // display_on_line(s, display, 4, "%s", display_store_and_contents(s, s->inst_aa));
	  // display_on_line(s, display, 5, "%s", display_register_and_contents(s, s->reginst_rc));
	  // display_on_line(s, display, 6, "%s", display_register_and_contents(s, s->reginst_rd));
	  break;
	  
	case 1:
	  // Store (R0) and (R1) in location Aa in data format; i.e. copy (R0)
	  // into the exponent position, and copy (RO into the sign and
	  // significant digit positions. If the number is outside the range
	  // that can be held in a storage location, set the ERROR indicator
	  // and stop

	  // Fixed registers
	  s->reginst_rc = 0;
	  s->reginst_rd = 1;

	  store_value = 0;
	  store_value = STORE_SET_EXPONENT(store_value, read_register(s, 0));
	  store_value = STORE_SET_SIGN(    store_value, SW_SIGN(read_register(s, 1)));
	  store_value = STORE_SET_DIGITS(  store_value, SW_DIGITS(read_register(s, 1)));
	  write_sw_to_store(s, s->inst_aa, store_value);
	  
#if DEBUG_INST_21
	  printf("\nINST 21");
	  printf("\nWriting %08X to store location %02X", store_value, s->inst_aa);
#endif

          next_iar(s);
	  // display_line_2(s, display);
	  // display_on_line(s, display, 3, "               ");
	  // display_on_line(s, display, 4, "%s", display_store_and_contents(s, s->inst_aa));
	  // display_on_line(s, display, 5, "%s", display_register_and_contents(s, s->reginst_rc));
	  // display_on_line(s, display, 6, "%s", display_register_and_contents(s, s->reginst_rd));
	  break;
	  
	case 2:
	  // Store (R0) and (R1) in location Aa in instruction format; i.e.
	  // copy (R0) into the left-hand four digit positions and (R1) into
	  // the right-hand four digit positions
          // Fixed registers
	  s->reginst_rc = 0;
	  s->reginst_rd = 1;

	  store_value = 0;
	  store_value = STORE_SET_LH4_DIGITS(store_value, read_register(s, 0));
	  store_value = STORE_SET_RH4_DIGITS(store_value, read_register(s, 1));
	  write_sw_to_store(s, s->inst_aa, store_value);
	  
#if DEBUG_INST_22
	  printf("\nINST 22");
	  printf("\nWriting %08X to store location %02X", store_value, s->inst_aa);
#endif

          next_iar(s);
	  // display_line_2(s, display);
	  // display_on_line(s, display, 3, "               ");
	  // display_on_line(s, display, 4, "%s", display_store_and_contents(s, s->inst_aa));
	  // display_on_line(s, display, 5, "%s", display_register_and_contents(s, s->reginst_rc));
	  // display_on_line(s, display, 6, "%s", display_register_and_contents(s, s->reginst_rd));
	  break;
	  
	case 4:
	  // Unconditional branch

	  // Calculate and store the link address
          s->iar = calculate_link_address(s->iar);
	  s->link_register = s->iar.address;
	  
	  // Now over-write that IAR with the address we want to jump to
          load_iar_bcd(s, s->inst_aa);

          //	  s->iar.address = s->inst_aa;

          s->iar.a_flag = 0;

	  // Unconditional branch
	  // IAR already set up.

	  // display_line_2(s, display);
	  // display_on_line(s, display, 3, "%s", display_store_and_contents(s, s->inst_aa));
	  break;

        case 5:
          // Branch if control latch is 1
          if( s->control_latch == 1 )
            {
#if DEBUG_BRANCH
              printf("\n25xx BRANCH");
#endif
              // Calculate and store the link address
              s->iar = calculate_link_address(s->iar);
              s->link_register = s->iar.address;
	  
              // Now over-write that IAR with the address we want to jump to
              //	      s->iar.address = s->inst_aa;
              load_iar_bcd(s, s->inst_aa);
              s->iar.a_flag = 0;
            }
          else
            {
              // Move to next IAR if test fails
              next_iar(s);
            }
      
          break;

        case 6:
      	  // Branch if control latch is 0
	  if( s->control_latch == 0 )
	    {
              // Calculate and store the link address
              s->iar = calculate_link_address(s->iar);
              s->link_register = s->iar.address;

	      // Now over-write that IAR with the address we want to jump to
              //	      s->iar.address = s->inst_aa;
              load_iar_bcd(s, s->inst_aa);
	      s->iar.a_flag = 0;
	    }
	  else
	    {
	      // Move to next IAR if test fails
	      next_iar(s);
	    }
          break;
      
        case 7:
      	  // Store contents of link address in Aa
	  write_sw_to_store(s, s->inst_aa, s->link_register);

          next_iar(s);
          break;

          // x8 and x9 done in stage B
#if 0          
        case 8:
      	  // Stop and when restarted transfer keyboard register contents into Aa
	  s->stop = 1;
	  s->on_restart_load_aa = 1;
          s->update_display = 1;
          
          next_iar(s);
          break;
          
        case 9:
      	  // Display
          next_iar(s);

	  // Stop and display (Aa)
	  s->stop = 1;
          break;
#endif
	}
      
      break;

    case 7:
    case 8:
    case 9:
      
#if EXTRACODE_FRAMEWORK
      // Put up stage B display, we have to force this display as we are running in the upper store after
      //entering extracode above.
      //      update_display();

      
      // Set up the extracode framework, if we aren't already in extracode
      // Extracode instructions aren't allowed in extracode subroutines
      if( !IS_EXTRACODE )
        {
          enter_extracode(s);
        }
      else
        {
          // Error
          enter_error_state(s, "Threee address instruction found in extracode subroutine");
        }
#else
      
#endif
      break;
    }

#if DEBUG_STAGES
  printf(" [Stage C: AUXIAR:%03X%s IAR:%03X%s] exit", s->aux_iar.address, s->aux_iar.a_flag?"A":" ", s->iar.address, s->iar.a_flag?"A":" ");
#endif

#if DUMP_STATE_STAGE_C
  cli_dump_state();
#endif

  // Stage C only displayed if we aren't in extracode
  // If we are then it is displayed when we exit
  if( !IS_EXTRACODE )
    {
      stage_c_display(s, display, s->inst_digit_a);
    }

  if( s->exiting_extracode && !s->run)
    {
#if DEBUG_EXTRACODE
      printf("\nExiting extracode...");
#endif
      
      // This is always displayed, so over-ride display setting
      stage_c_display(s, DISPLAY_UPDATE, s->inst_digit_a);

      // Not exiting any more
      s->exiting_extracode = 0;
    }
  
  FN_EXIT;
  
}

////////////////////////////////////////////////////////////////////////////////
// Stage B
// Decode absolute addresses
// Execute if possible
////////////////////////////////////////////////////////////////////////////////

void stage_b_decode(ESC_STATE *s, int display)
{
  FN_ENTRY_DISPLAY;
  int display_override = display;
  
#if DEBUG_STAGES
  printf(" [Stage B: AUXIAR:%03X%s IAR:%03X%s] ", s->aux_iar.address, s->aux_iar.a_flag?"A":" ", s->iar.address, s->iar.a_flag?"A":" ");
#endif

  switch(s->inst_digit_a)
    {
    case 2:
    case 3:
    case 4:
    case 5:
    case 6:
      switch(s->inst_digit_b)
	{
        case 8:
      	  // Stop and when restarted transfer keyboard register contents into Aa
          // Only stop if we aren't in an extracode subroutine and running the instruction
          // action. 

          if( s->run, 1 )
            {
              s->stop = 1;
            }

	  s->on_restart_load_aa = 1;
          s->update_display = 1;
          display_override = DISPLAY_UPDATE;
          next_iar(s);
          break;
          
        case 9:
      	  // Display
          next_iar(s);

	  // Stop and display (Aa)
          // If running extracode we don't stop, but use the stage step stops
          if( s->run,1 )
            {
              s->stop = 1;
            }
          display_override = DISPLAY_UPDATE;
          break;

	}
      
      break;
    }
  
  stage_b_display(s, display_override, s->inst_digit_a);
  
  FN_EXIT;
}

////////////////////////////////////////////////////////////////////////////////
//
// Display for stage A
//
////////////////////////////////////////////////////////////////////////////////

// Display varies sightly depending on instruction field a

void stage_a_display(ESC_STATE *s, int display, int a)
{
  // Common Items

  clear_display(s, display);
  
  // Top line clear
  clear_line(s, display, 1);

  display_line_2(s, display);
  clear_line(s, display, 3);
  
  switch(a)
    {
      // Register instructions
    case 0:
      switch(s->inst_digit_b)
	{
	case 0:
	case 1:
	case 2:
	case 3:

        case 5:
        case 6:
        case 7:
	  display_line_2(s, display);
	  clear_lines_3_to_6(s, display);
	  display_any_size_register_on_line(s, display, 3, s->reginst_rc, NO_CONTENTS);
          break;
        }
      
    case 1:
      display_line_2(s, display);
      clear_lines_3_to_6(s, display);
      display_two_any_size_register_on_line(s, display, 3, s->reginst_rc, s->reginst_rd, NO_CONTENTS);
      break;

    case 2:
    case 3:
    case 4:
    case 5:
    case 6:
      switch(s->inst_digit_b)
	{
	case 0:
	case 1:
	case 2:
	  display_line_2(s, display);
          display_on_line(s, display, 3, "%2X    %s", s->inst_ap, display_store_word(load_from_store(s, s->inst_ap)));
	  display_any_size_register_on_line(s, display, 4, 0, NO_CONTENTS);
          display_any_size_register_on_line(s, display, 5, 1, NO_CONTENTS);
          break;
          
        case 4:
        case 5:
        case 6:
        case 7:
        case 8:
        case 9:
	  display_line_2(s, display);
          display_on_line(s, display, 3, "%2X    %s", s->inst_ap, display_store_word(load_from_store(s, s->inst_ap)));
          break;
        }
      
      break;
      
      // Absolute addressing
    case 7:
      clear_line(s, display, 4);
      clear_line(s, display, 5);
      clear_line(s, display, 6);
      break;
      
      // Relative
    case 8:
      display_any_size_register_on_line(s, display, 4, 3, CONTENTS);
      display_any_size_register_on_line(s, display, 5, 4, CONTENTS);
      display_any_size_register_on_line(s, display, 6, 5, CONTENTS);
      break;

      // Indirect
    case 9:

      display_on_line(s, display, 4, "%2X    %s", s->Ap1, display_store_word(load_from_store(s, s->Ap1)));
      display_on_line(s, display, 5, "%2X    %s", s->Ap2, display_store_word(load_from_store(s, s->Ap2)));
      display_on_line(s, display, 6, "%2X    %s", s->Ap3, display_store_word(load_from_store(s, s->Ap3)));
      break;
    }
}

////////////////////////////////////////////////////////////////////////////////
//
// Display for stage B
//
////////////////////////////////////////////////////////////////////////////////


void stage_b_display(ESC_STATE *s, int display, int a)
{
  // Common Items
  FN_ENTRY;
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
